stefanhepp/eOrgan/design/parts/Powerswitch Case.FCStd

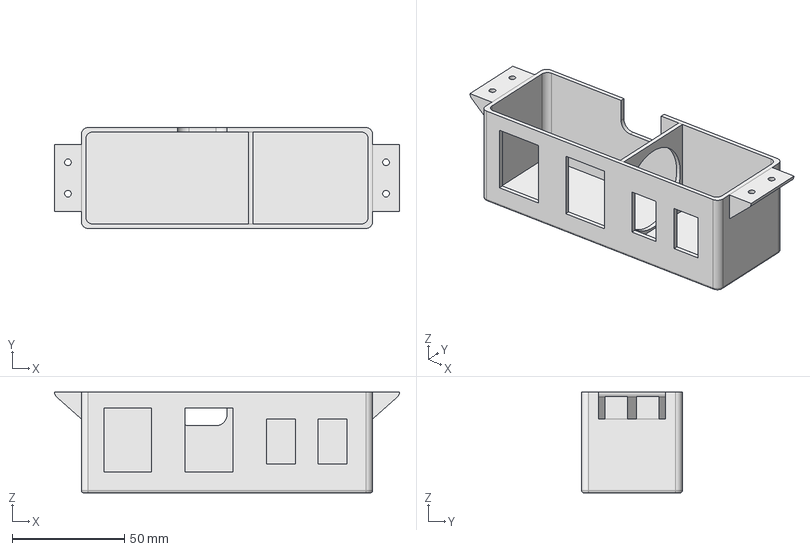
[picture p15: CAD file, 2022-12-17]
design/parts/Powerswitch Case.FCStd
154.0 x 45.0 x 45.0 mm
