stefanhepp/eOrgan/design/parts/Interface Case.FCStd

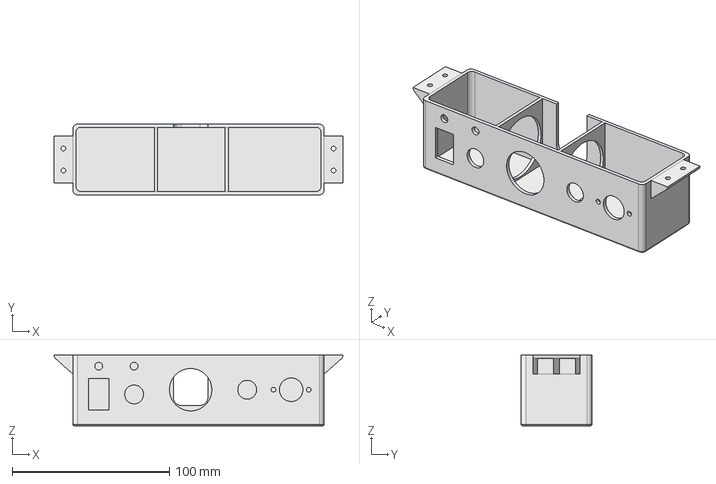
[picture p16: CAD file, 2022-12-17]
design/parts/Interface Case.FCStd
184.0 x 45.0 x 45.0 mm
