stefanhepp/eOrgan/design/parts/Doorknob.FCStd

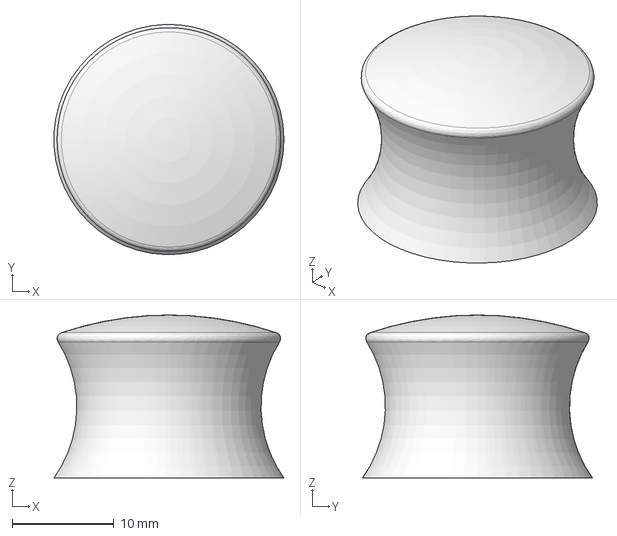
[picture p17: CAD file, 2022-12-17]
design/parts/Doorknob.FCStd
22.6 x 22.6 x 16.0 mm
