stefanhepp/eOrgan/design/parts/Toestop Switch.FCStd

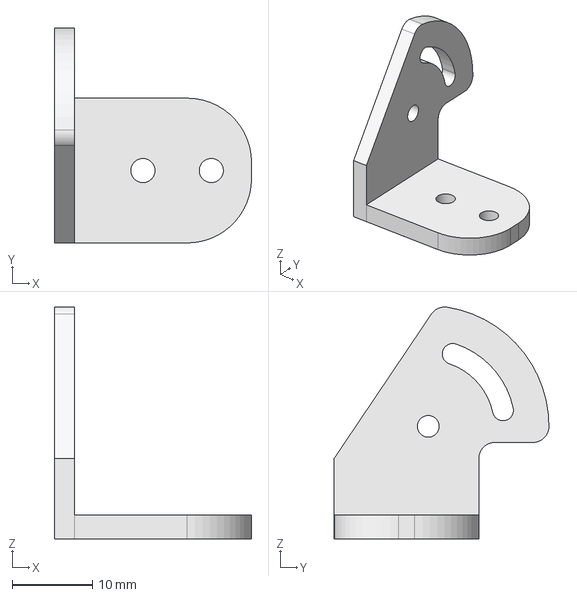
[picture p18: CAD file, 2022-12-17]
design/parts/Toestop Switch.FCStd
24.5 x 26.7 x 28.8 mm
