stefanhepp/eOrgan/design/Panel Inserts.FCStd

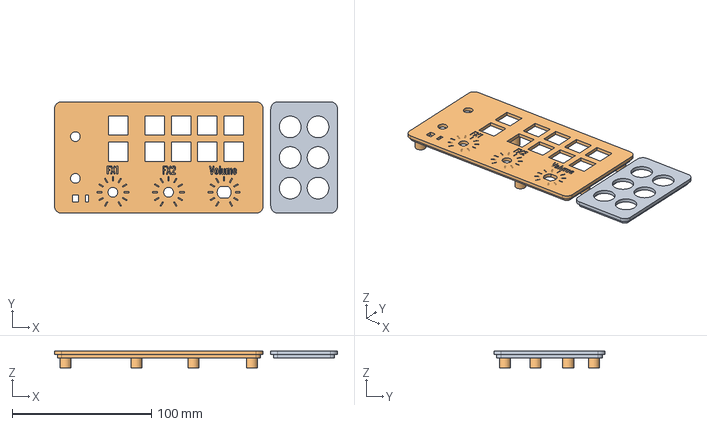
[picture p19: CAD file, 2024-10-20]
design/Panel Inserts.FCStd
203.5 x 80.0 x 12.0 mm
Buttons
MainControl
