stefanhepp/eOrgan/design/Panel Inserts-Buttons.step

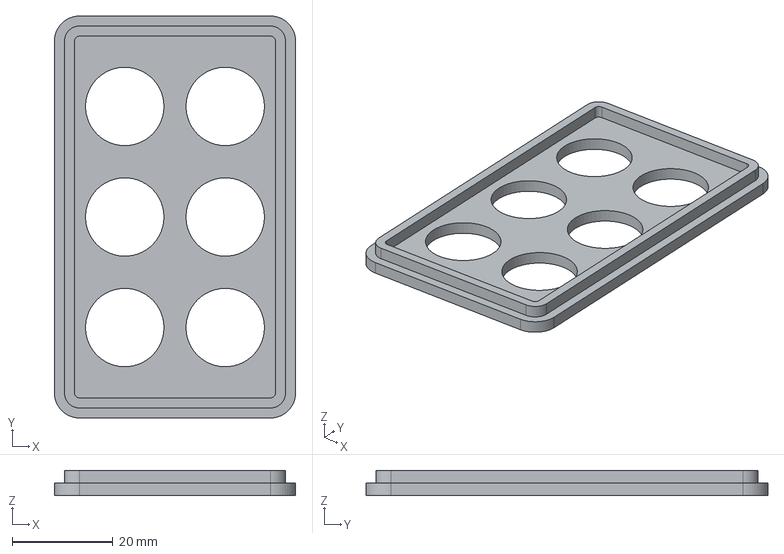
[picture p20: CAD file, 2024-10-18]
design/Panel Inserts-Buttons.step
48.0 x 80.0 x 5.00 mm
