stefanhepp/eOrgan/design/Lock Mount-Body Left.step

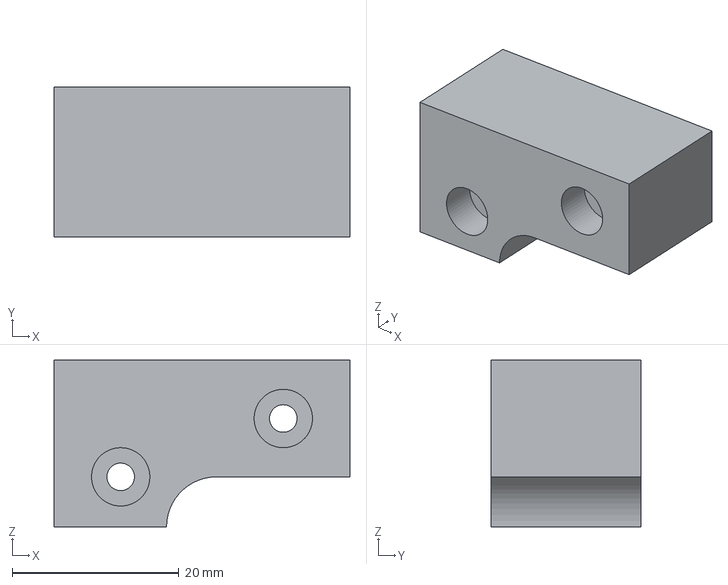
[picture p21: CAD file, 2024-10-08]
design/Lock Mount-Body Left.step
35.5 x 18.0 x 20.0 mm
