stefanhepp/eOrgan/design/Lock Mount-Body Right.step

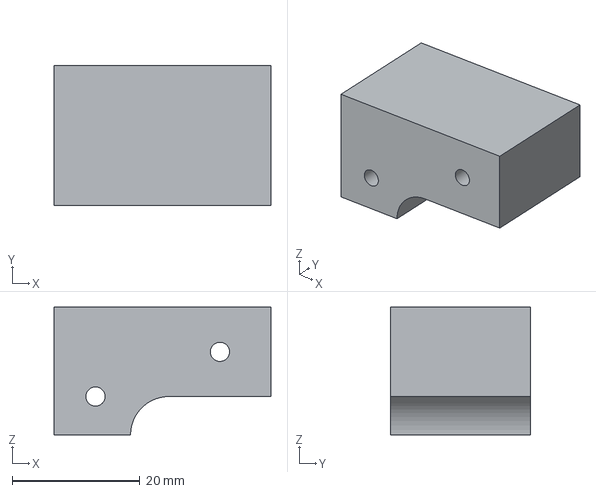
[picture p22: CAD file, 2024-10-08]
design/Lock Mount-Body Right.step
34.0 x 22.0 x 20.0 mm
