stefanhepp/eOrgan/design/PCB Holder.FCStd

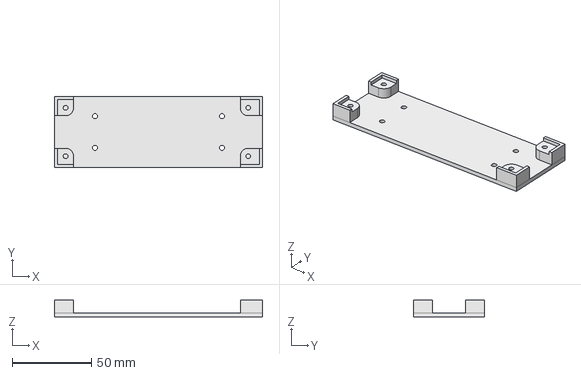
[picture p23: CAD file, 2024-09-07]
design/PCB Holder.FCStd
131.0 x 44.5 x 10.5 mm
