stefanhepp/eOrgan/design/PCB Holder-Technics.step

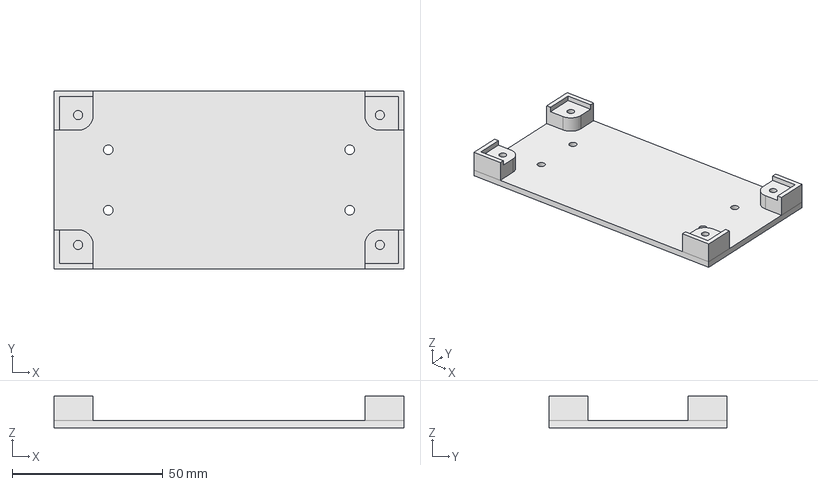
[picture p24: CAD file, 2024-09-07]
design/PCB Holder-Technics.step
116.0 x 59.0 x 10.5 mm
