stefanhepp/eOrgan/design/PCB Holder-LCD.step

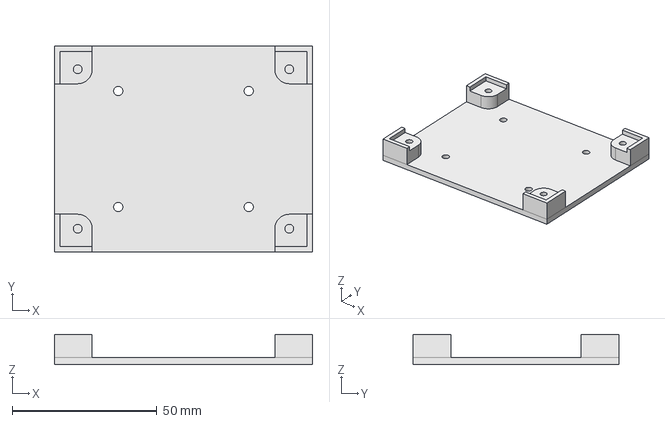
[picture p25: CAD file, 2024-09-07]
design/PCB Holder-LCD.step
89.0 x 71.0 x 10.5 mm
