stefanhepp/eOrgan/design/PCB Holder-150x100.step

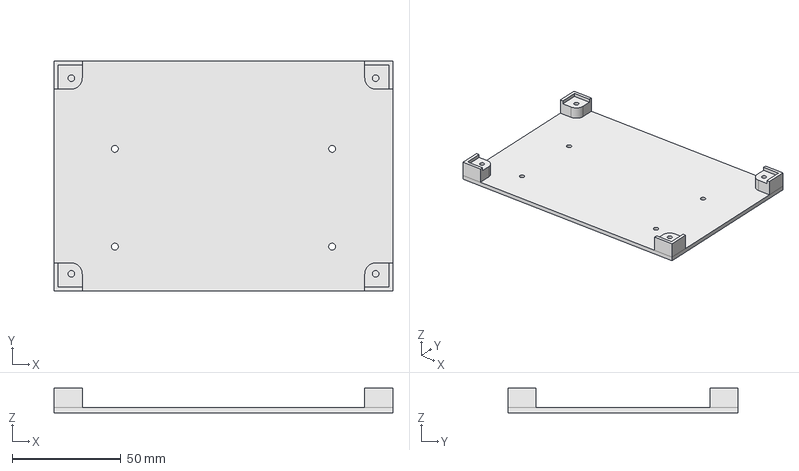
[picture p26: CAD file, 2024-09-07]
design/PCB Holder-150x100.step
156.0 x 106.0 x 11.5 mm
