stefanhepp/eOrgan/design/PCB Holder Technics-Holder 110x53.step

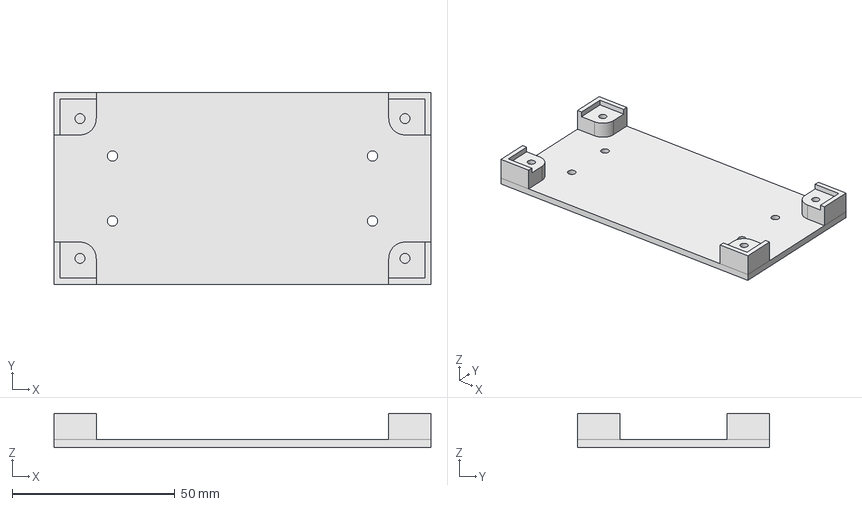
[picture p27: CAD file, 2024-09-02]
design/PCB Holder Technics-Holder 110x53.step
116.0 x 59.0 x 10.5 mm
