stefanhepp/eOrgan/design/ToeStudEncoder Case.FCStd

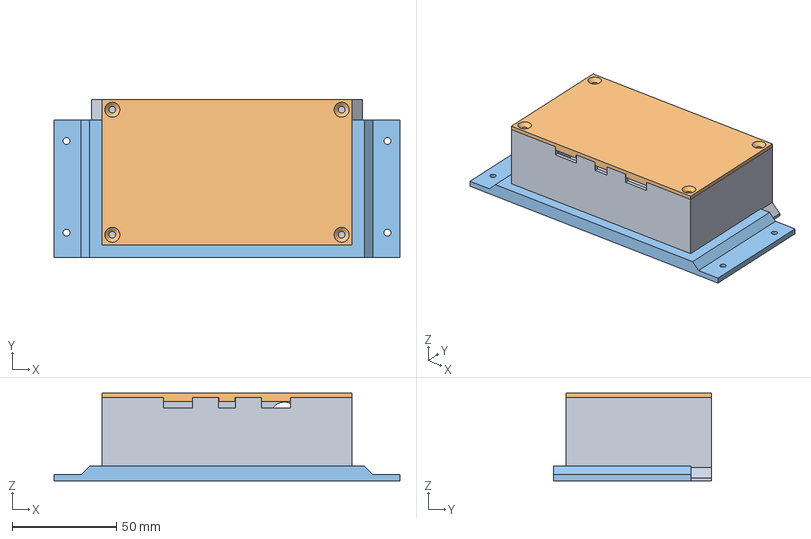
[picture p28: CAD file, 2024-06-30]
design/ToeStudEncoder Case.FCStd
166.0 x 76.0 x 42.0 mm
Case
Lid
Holder
