stefanhepp/eOrgan/design/ToeStudEncoder Case-Lid.step

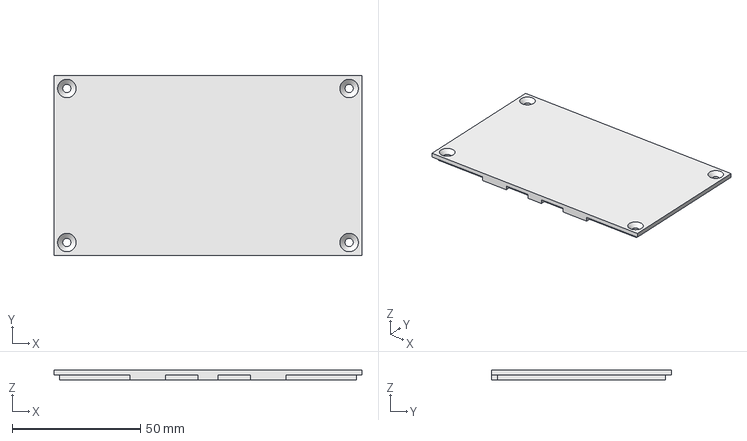
[picture p29: CAD file, 2024-06-30]
design/ToeStudEncoder Case-Lid.step
120.0 x 70.0 x 4.00 mm
