stefanhepp/eOrgan/design/ToeStudEncoder Case-Case.step

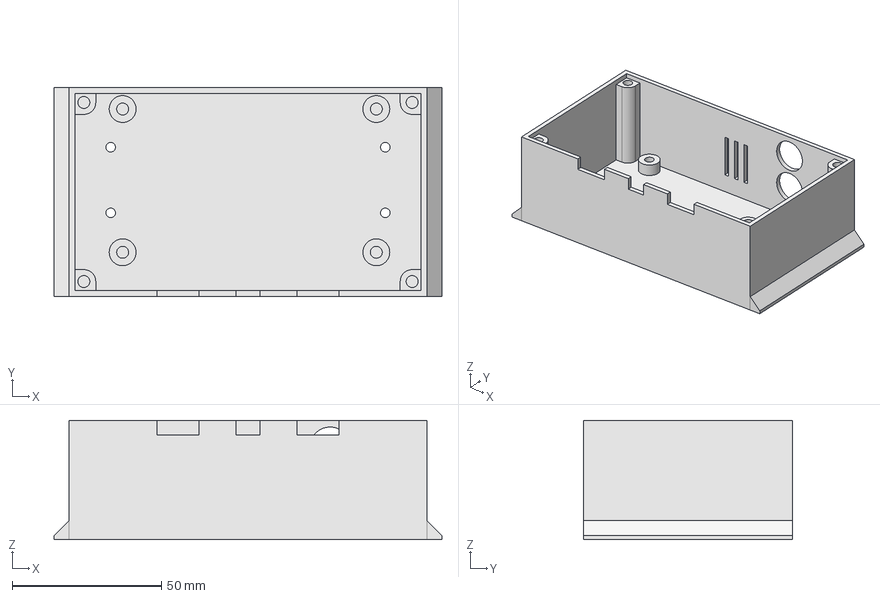
[picture p30: CAD file, 2024-06-30]
design/ToeStudEncoder Case-Case.step
130.0 x 70.0 x 40.0 mm
