stefanhepp/eOrgan/design/ToeStudEncoder Case-Holder.step

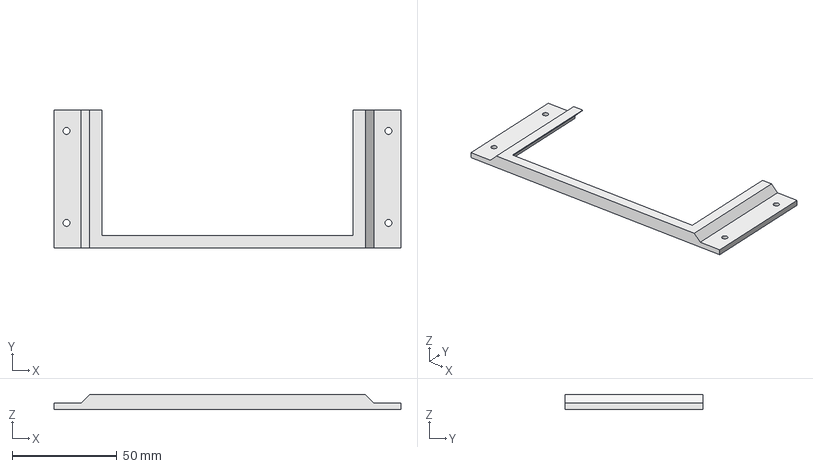
[picture p31: CAD file, 2024-06-30]
design/ToeStudEncoder Case-Holder.step
166.0 x 66.0 x 7.00 mm
