stefanhepp/eOrgan/design/PCB Holder-Base.step

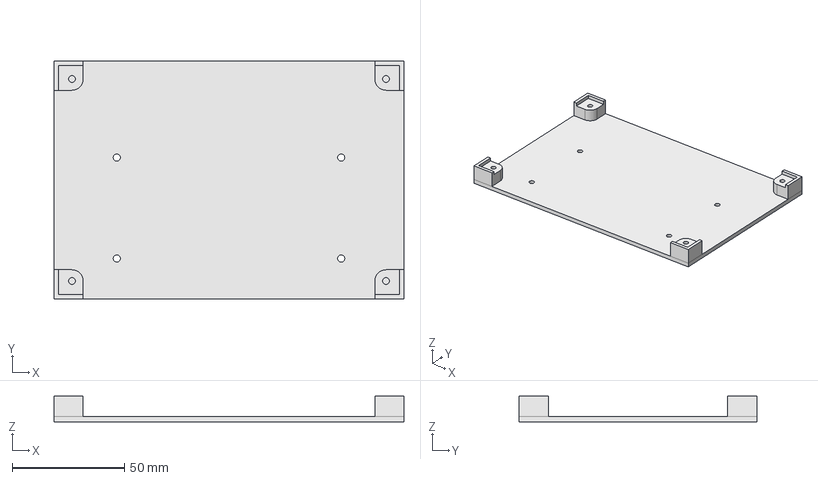
[picture p32: CAD file, 2024-06-30]
design/PCB Holder-Base.step
156.0 x 106.0 x 11.5 mm
