stefanhepp/eOrgan/boards/MIDIController-IO-Boards/MIDIController-IO-Boards.kicad_pcb

## KiCad design boards/MIDIController-IO-Boards/MIDIController-IO-Boards.kicad_pcb (2024-06-30)

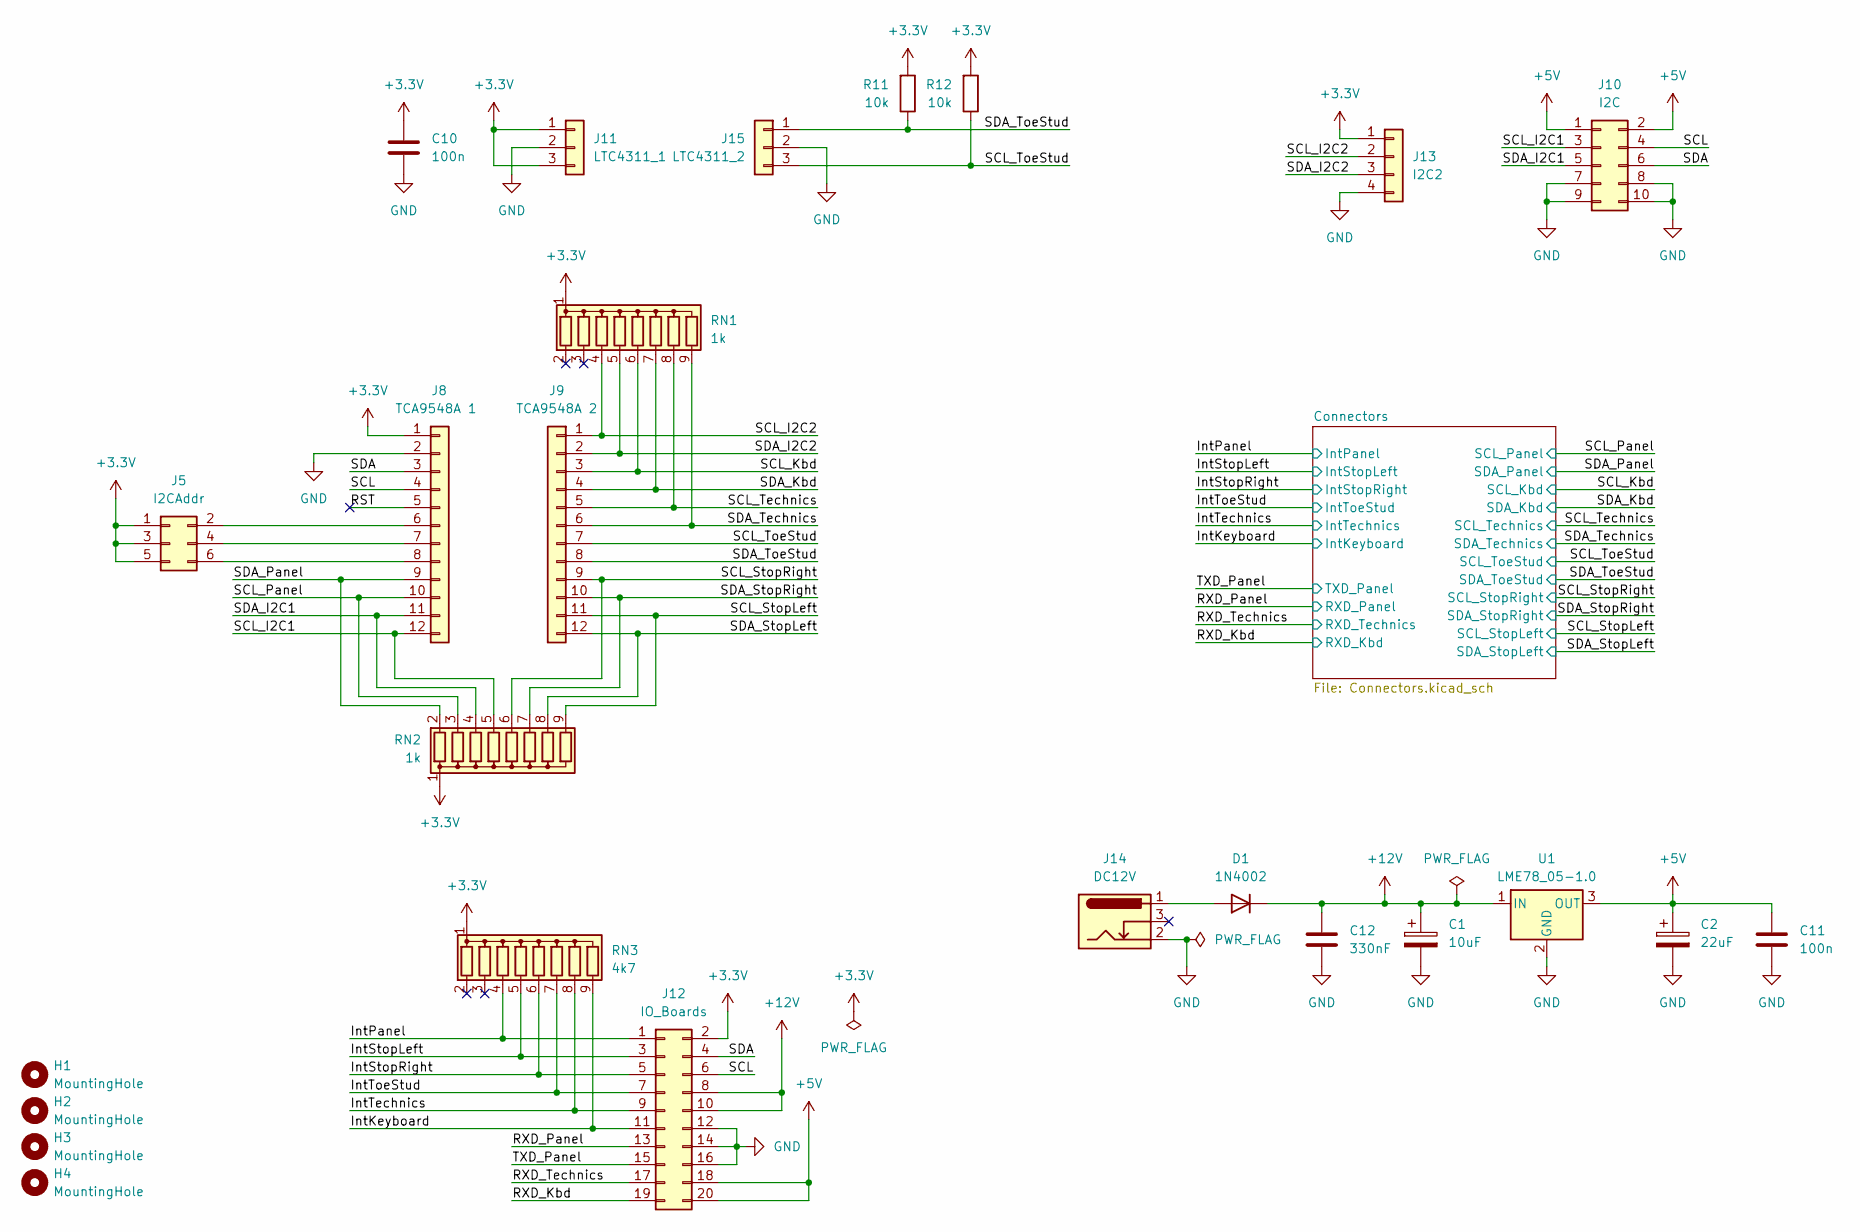
[picture p56: schematic MIDIController-IO-Boards.kicad_sch]

Parts:
C1: 10uF; CP_Radial_D5.0mm_P2.00mm
C2: 22uF; CP_Radial_D8.0mm_P2.50mm
C10, C11: 100n; C_Disc_D5.0mm_W2.5mm_P5.00mm
C12: 330nF; C_Disc_D5.0mm_W2.5mm_P5.00mm
D1: 1N4002; D_DO-41_SOD81_P10.16mm_Horizontal
H1, H2, H3, H4: MountingHole; MountingHole_3.2mm_M3
J5: I2CAddr; PinHeader_2x03_P2.54mm_Vertical
J8: TCA9548A 1; PinSocket_1x12_P2.54mm_Vertical
J9: TCA9548A 2; PinSocket_1x12_P2.54mm_Vertical
J10: I2C; IDC-Header_2x05_P2.54mm_Vertical
J11: LTC4311_1; PinSocket_1x03_P2.54mm_Vertical
J12: IO_Boards; IDC-Header_2x10_P2.54mm_Vertical
J13: I2C2; PinHeader_1x04_P2.54mm_Vertical
J14: DC12V; BarrelJack_Horizontal
J15: LTC4311_2; PinSocket_1x03_P2.54mm_Vertical
R11, R12: 10k; R_Axial_DIN0207_L6.3mm_D2.5mm_P10.16mm_Horizontal
RN1, RN2: 1k; R_Array_SIP9
RN3: 4k7; R_Array_SIP9
U1: LME78_05-1.0; Converter_DCDC_GAPTEC_LME78_05-1.0

Connections:
+3.3V: C10.1, J5.1, J5.3, J5.5, J8.1, J11.1, J11.3, J12.2, J13.1, R11.2, R12.2, RN1.1 (common), RN2.1 (common), RN3.1 (common); also elsewhere on the board
+5V: C2.1, C11.1, J10.1, J10.2, J12.18, J12.20, U1.3 (OUT); also elsewhere on the board
+12V: C1.1, C12.1, D1.1 (K), J12.8, J12.10, U1.1 (IN); also elsewhere on the board
/IntKeyboard: J12.11, RN3.9 (R8); also elsewhere on the board
/IntPanel: J12.1, RN3.4 (R3); also elsewhere on the board
/IntStopLeft: J12.3, RN3.5 (R4); also elsewhere on the board
/IntStopRight: J12.5, RN3.6 (R5); also elsewhere on the board
/IntTechnics: J12.9, RN3.8 (R7); also elsewhere on the board
/IntToeStud: J12.7, RN3.7 (R6); also elsewhere on the board
/RST: J8.5
/RXD_Kbd: J12.19; also elsewhere on the board
/RXD_Panel: J12.13; also elsewhere on the board
/RXD_Technics: J12.17; also elsewhere on the board
/SCL: J8.4, J10.4, J12.6
/SCL_I2C1: J8.12, J10.3, RN2.5 (R4)
/SCL_I2C2: J9.1, J13.2, RN1.4 (R3)
/SCL_Kbd: J9.3, RN1.6 (R5); also elsewhere on the board
/SCL_Panel: J8.10, RN2.3 (R2); also elsewhere on the board
/SCL_StopLeft: J9.11, RN2.9 (R8); also elsewhere on the board
/SCL_StopRight: J9.9, RN2.6 (R5); also elsewhere on the board
/SCL_Technics: J9.5, RN1.8 (R7); also elsewhere on the board
/SCL_ToeStud: J9.7, J15.3, R12.1; also elsewhere on the board
/SDA: J8.3, J10.6, J12.4
/SDA_I2C1: J8.11, J10.5, RN2.4 (R3)
/SDA_I2C2: J9.2, J13.3, RN1.5 (R4)
/SDA_Kbd: J9.4, RN1.7 (R6); also elsewhere on the board
/SDA_Panel: J8.9, RN2.2 (R1); also elsewhere on the board
/SDA_StopLeft: J9.12, RN2.8 (R7); also elsewhere on the board
/SDA_StopRight: J9.10, RN2.7 (R6); also elsewhere on the board
/SDA_Technics: J9.6, RN1.9 (R8); also elsewhere on the board
/SDA_ToeStud: J9.8, J15.1, R11.1; also elsewhere on the board
/TXD_Panel: J12.15; also elsewhere on the board
GND: C1.2, C2.2, C10.2, C11.2, C12.2, J8.2, J10.7, J10.8, J10.9, J10.10, J11.2, J12.12, J12.14, J12.16, J13.4, J14.2, J15.2, U1.2 (GND); also elsewhere on the board
unnamed: D1.2 (A), J14.1
unnamed: J5.2, J8.6
unnamed: J5.4, J8.7
unnamed: J5.6, J8.8

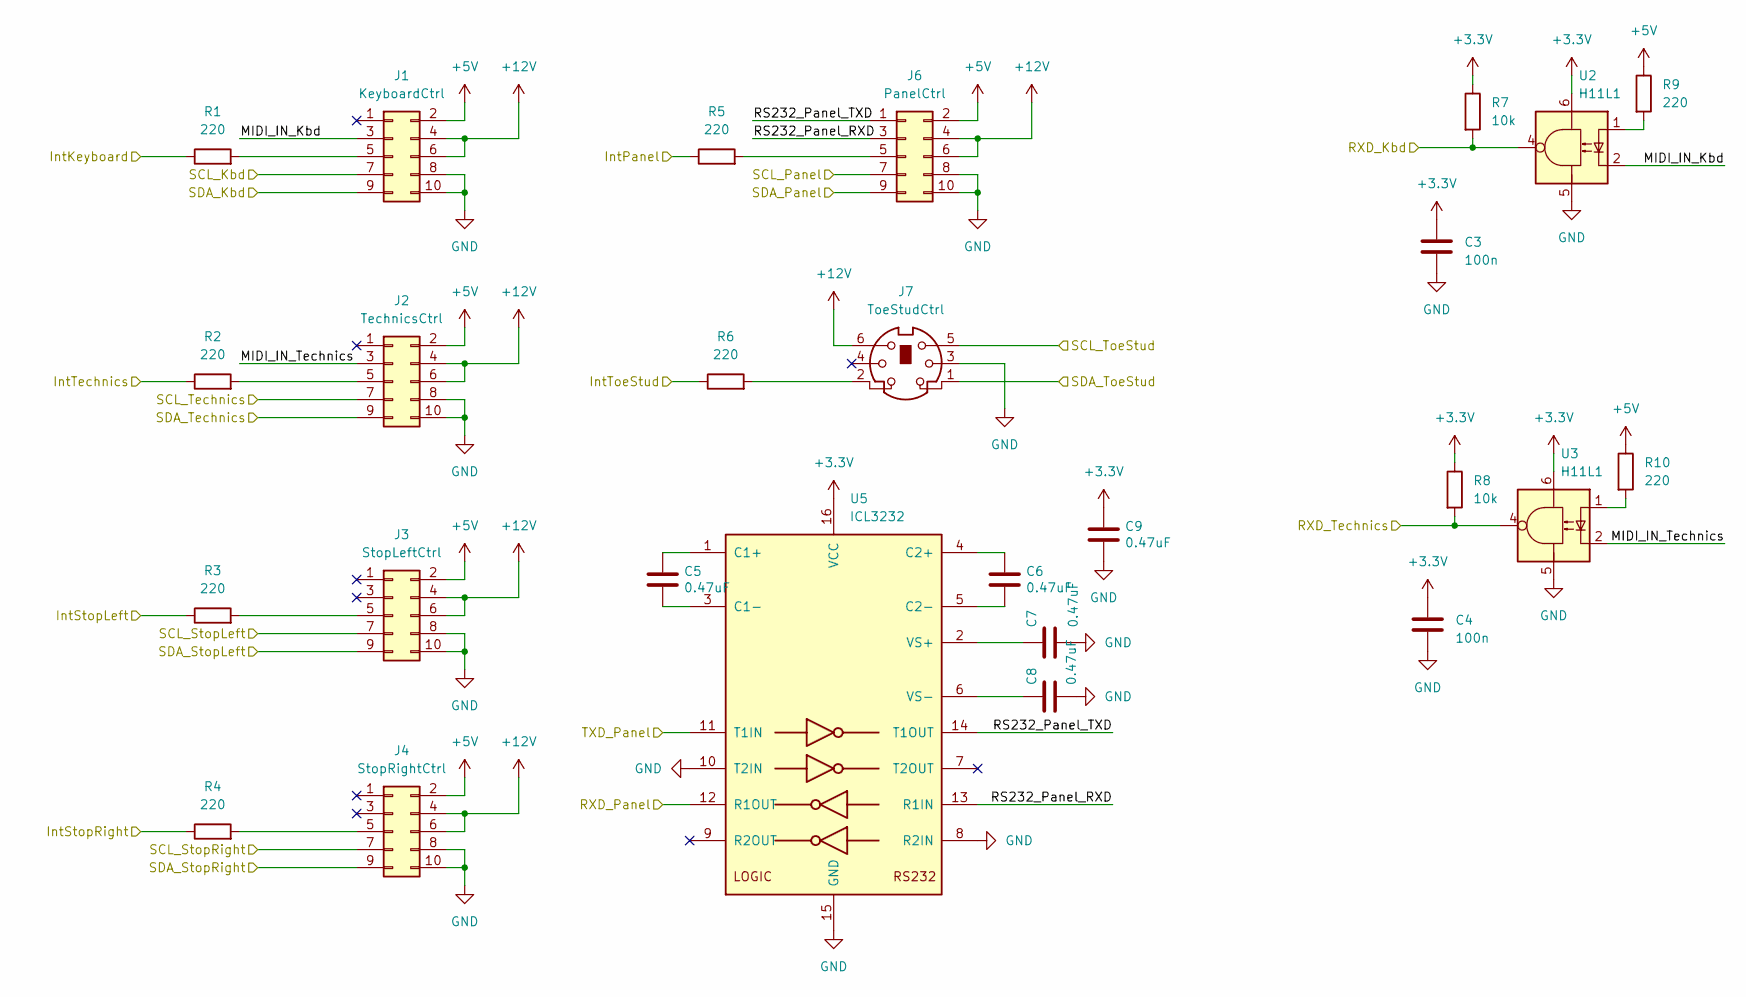
[picture p57: schematic Connectors.kicad_sch]

Parts:
C3, C4: 100n; C_Disc_D5.0mm_W2.5mm_P5.00mm
C5, C6, C7, C8, C9: 0.47uF; C_Rect_L7.0mm_W3.5mm_P5.00mm; Voltage 50V
J1: KeyboardCtrl; IDC-Header_2x05_P2.54mm_Horizontal
J2: TechnicsCtrl; IDC-Header_2x05_P2.54mm_Horizontal
J3: StopLeftCtrl; IDC-Header_2x05_P2.54mm_Horizontal
J4: StopRightCtrl; IDC-Header_2x05_P2.54mm_Horizontal
J6: PanelCtrl; IDC-Header_2x05_P2.54mm_Horizontal
J7: ToeStudCtrl; MiniDIN TE_5749180-1
R1, R2, R3, R4, R5, R6, R9, R10: 220; R_Axial_DIN0207_L6.3mm_D2.5mm_P10.16mm_Horizontal
R7, R8: 10k; R_Axial_DIN0207_L6.3mm_D2.5mm_P10.16mm_Horizontal
U2, U3: H11L1; DIP-6_W7.62mm
U5: ICL3232; DIP-16_W7.62mm

Connections:
+3.3V: C3.1, C4.1, C9.1, R7.1, R8.1, U2.6, U3.6, U5.16 (VCC); also elsewhere on the board
+5V: J1.2, J2.2, J3.2, J4.2, J6.2, R9.1, R10.1; also elsewhere on the board
+12V: J1.4, J1.6, J2.4, J2.6, J3.4, J3.6, J4.4, J4.6, J6.4, J6.6, J7.6; also elsewhere on the board
/Connectors/MIDI_IN_Kbd: J1.3, U2.2
/Connectors/MIDI_IN_Technics: J2.3, U3.2
/Connectors/RS232_Panel_RXD: J6.3, U5.13 (R1IN)
/Connectors/RS232_Panel_TXD: J6.1, U5.14 (T1OUT)
/IntKeyboard: R1.1; also elsewhere on the board
/IntPanel: R5.1; also elsewhere on the board
/IntStopLeft: R3.1; also elsewhere on the board
/IntStopRight: R4.1; also elsewhere on the board
/IntTechnics: R2.1; also elsewhere on the board
/IntToeStud: R6.1; also elsewhere on the board
/RXD_Kbd: R7.2, U2.4; also elsewhere on the board
/RXD_Panel: U5.12 (R1OUT); also elsewhere on the board
/RXD_Technics: R8.2, U3.4; also elsewhere on the board
/SCL_Kbd: J1.7; also elsewhere on the board
/SCL_Panel: J6.7; also elsewhere on the board
/SCL_StopLeft: J3.7; also elsewhere on the board
/SCL_StopRight: J4.7; also elsewhere on the board
/SCL_Technics: J2.7; also elsewhere on the board
/SCL_ToeStud: J7.5; also elsewhere on the board
/SDA_Kbd: J1.9; also elsewhere on the board
/SDA_Panel: J6.9; also elsewhere on the board
/SDA_StopLeft: J3.9; also elsewhere on the board
/SDA_StopRight: J4.9; also elsewhere on the board
/SDA_Technics: J2.9; also elsewhere on the board
/SDA_ToeStud: J7.1; also elsewhere on the board
/TXD_Panel: U5.11 (T1IN); also elsewhere on the board
GND: C3.2, C4.2, C7.2, C8.2, C9.2, J1.8, J1.10, J2.8, J2.10, J3.8, J3.10, J4.8, J4.10, J6.8, J6.10, J7.3, U2.5, U3.5, U5.8 (R2IN), U5.10 (T2IN), U5.15 (GND); also elsewhere on the board
unnamed: J1.5, R1.2
unnamed: J2.5, R2.2
unnamed: J3.5, R3.2
unnamed: J4.5, R4.2
unnamed: J6.5, R5.2
unnamed: J7.2, R6.2
unnamed: R9.2, U2.1
unnamed: R10.2, U3.1
unnamed: C5.1, U5.1 (C1+)
unnamed: C5.2, U5.3 (C1-)
unnamed: C6.1, U5.4 (C2+)
unnamed: C6.2, U5.5 (C2-)
unnamed: C7.1, U5.2 (VS+)
unnamed: C8.1, U5.6 (VS-)

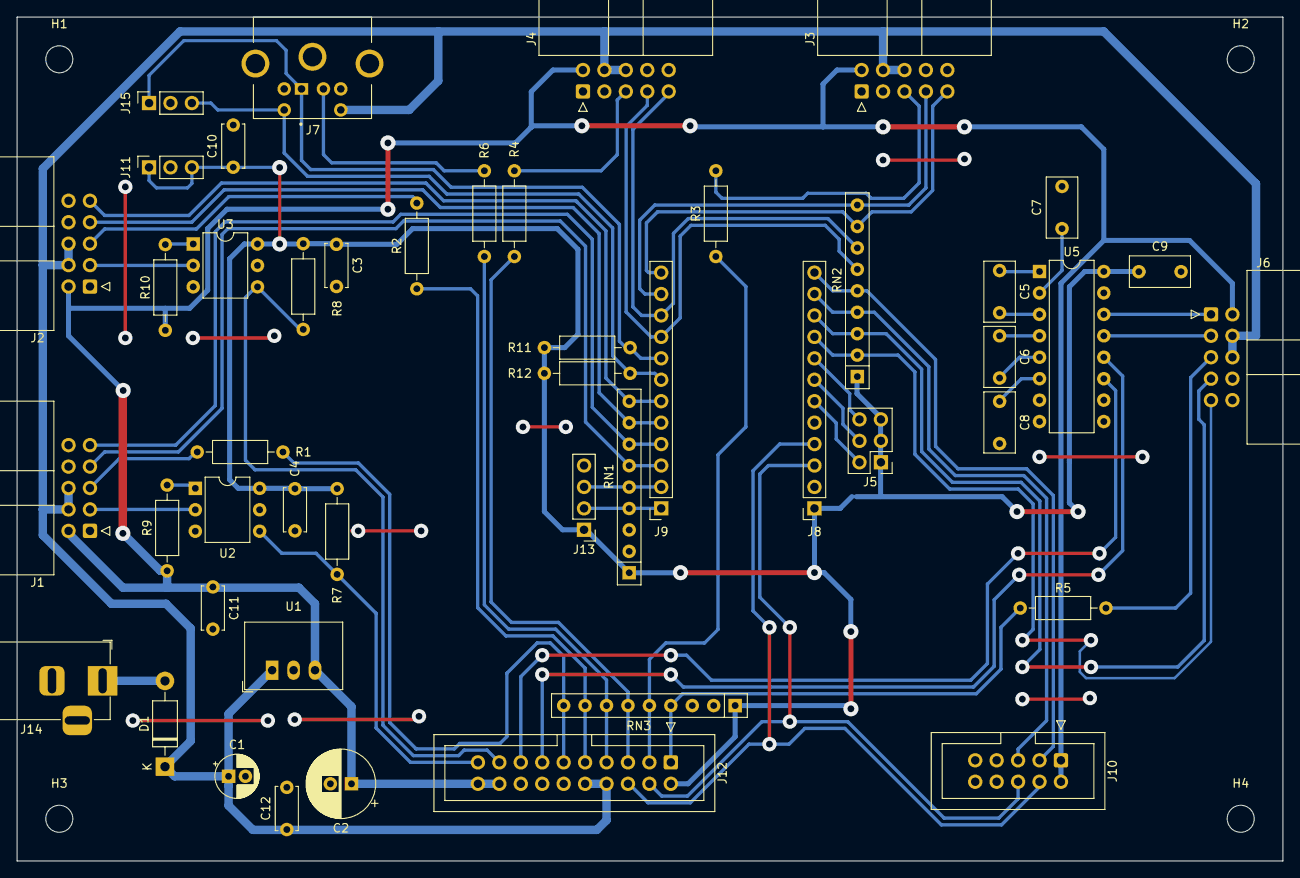
[picture p58: board MIDIController-IO-Boards.kicad_pcb from above]

Board: 2 copper layers, 150.0 x 100.0 mm, 51 parts (0 on the bottom side), 54 nets.
