stefanhepp/eOrgan/boards/KeyboardEncoder/KeyboardEncoder.kicad_pcb

## KiCad design boards/KeyboardEncoder/KeyboardEncoder.kicad_pcb (2024-05-18)

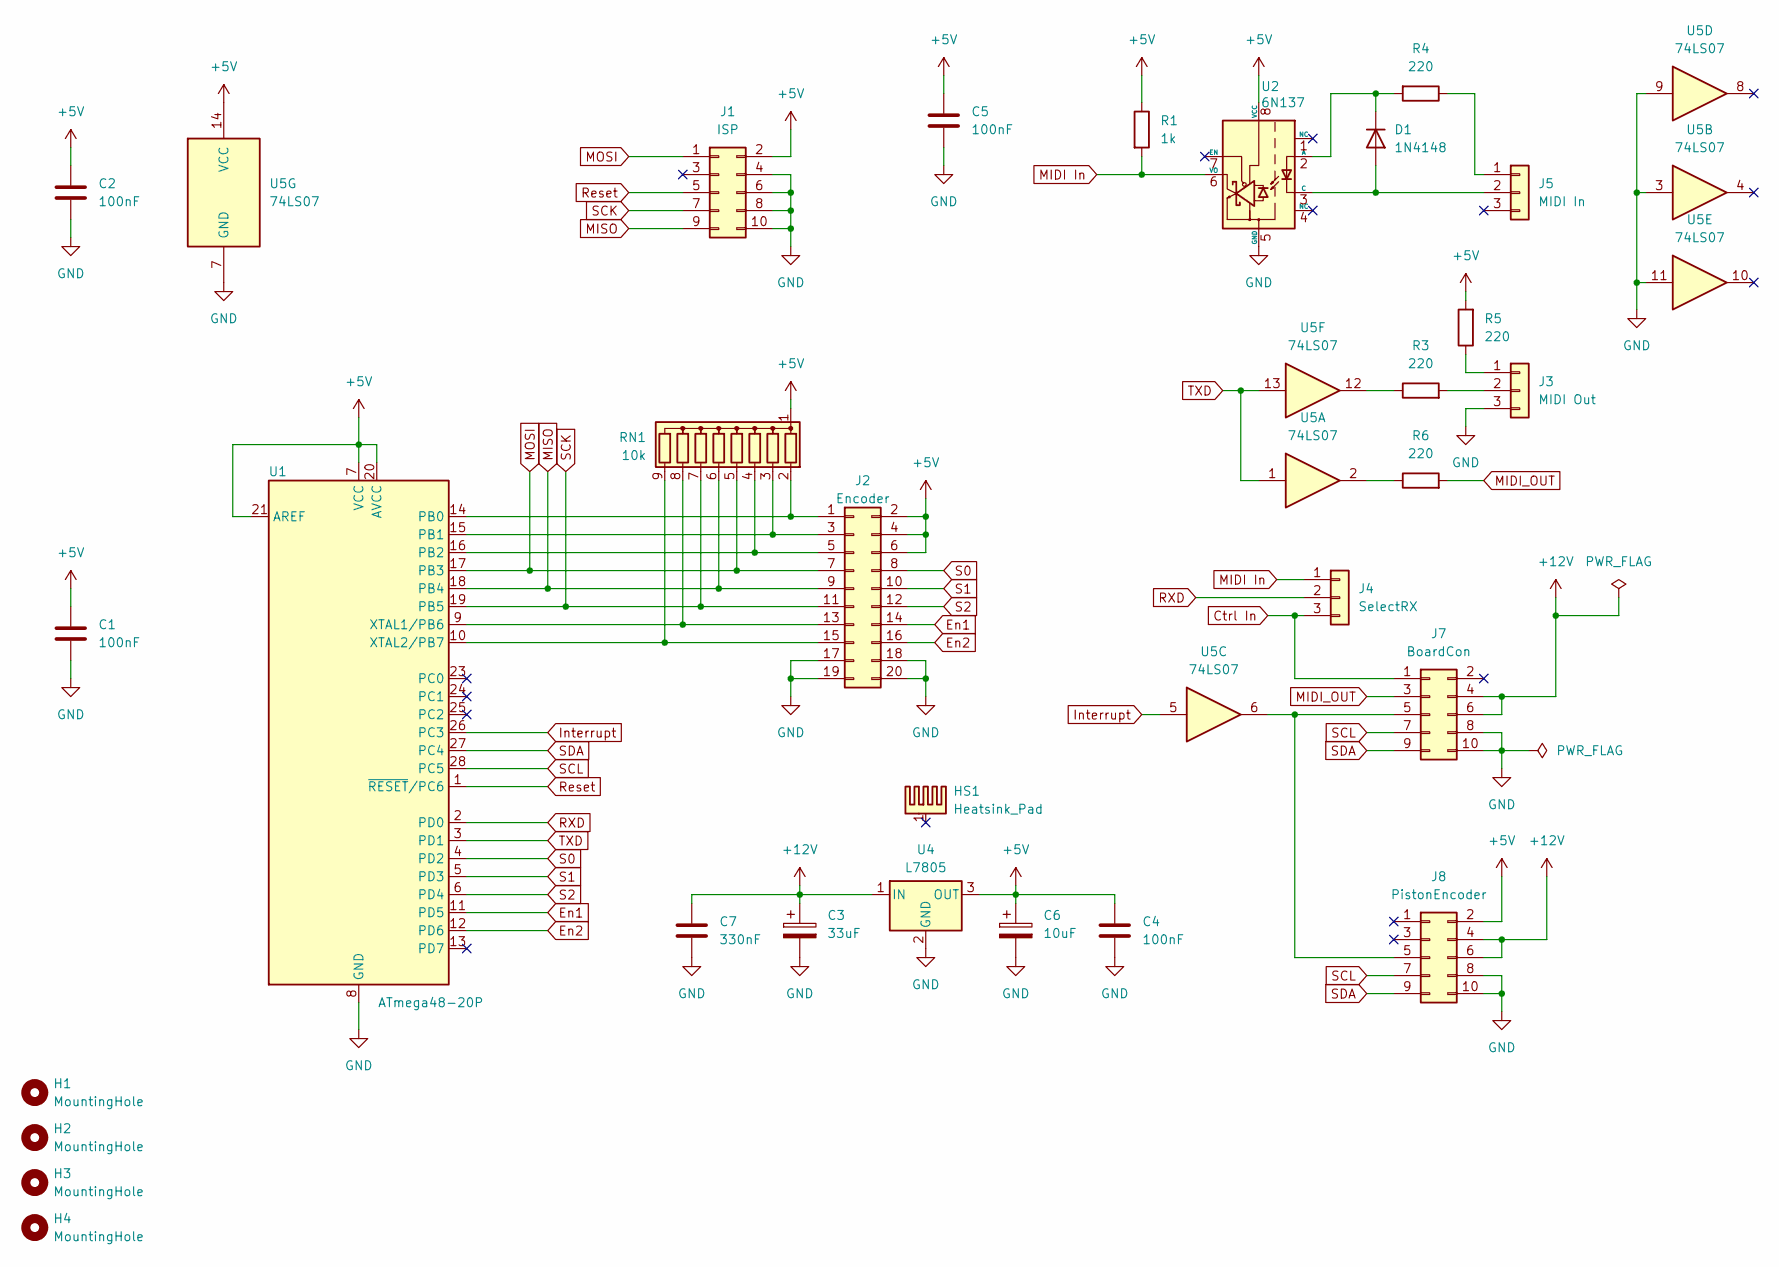
[picture p59: schematic KeyboardEncoder.kicad_sch]

Parts:
C1, C2, C4, C5: 100nF; C_Disc_D4.3mm_W1.9mm_P5.00mm
C3: 33uF; CP_Radial_D7.5mm_P2.50mm
C6: 10uF; CP_Radial_D5.0mm_P2.00mm
C7: 330nF; C_Disc_D4.3mm_W1.9mm_P5.00mm
D1: 1N4148; D_DO-35_SOD27_P7.62mm_Horizontal
H1, H2, H3, H4: MountingHole; MountingHole_3.2mm_M3
HS1: Heatsink_Pad; Heatsink_Aavid_TO-220_H12.7mm
J1: ISP; IDC-Header_2x05_P2.54mm_Horizontal
J2: Encoder; IDC-Header_2x10_P2.54mm_Horizontal
J3: MIDI Out; PinHeader_1x03_P2.54mm_Vertical
J4: SelectRX; PinHeader_1x03_P2.54mm_Vertical
J5: MIDI In; PinHeader_1x03_P2.54mm_Vertical
J7: BoardCon; IDC-Header_2x05_P2.54mm_Horizontal
J8: PistonEncoder; IDC-Header_2x05_P2.54mm_Vertical
R1: 1k; R_Axial_DIN0207_L6.3mm_D2.5mm_P2.54mm_Vertical
R3, R4, R5, R6: 220; R_Axial_DIN0207_L6.3mm_D2.5mm_P10.16mm_Horizontal
RN1: 10k; R_Array_SIP9
U1: ATmega48-20P; DIP-28_W7.62mm
U2: 6N137; DIP-8_W7.62mm
U4: L7805; TO-220-3_Vertical
U5: 74LS07; DIP-14_W7.62mm

Connections:
+5V: C1.1, C2.1, C4.1, C5.1, C6.1, J1.2, J2.2, J2.4, J2.6, J8.2, R1.1, R5.2, RN1.1 (common), U1.7 (VCC), U1.20 (AVCC), U1.21 (AREF), U2.8 (VCC), U4.3 (OUT), U5.14 (VCC)
+12V: C3.1, C7.1, J7.4, J7.6, J8.4, J8.6, U4.1 (IN)
Ctrl In: J4.3, J7.1
En1: J2.14, U1.11 (PD5)
En2: J2.16, U1.12 (PD6)
GND: C1.2, C2.2, C3.2, C4.2, C5.2, C6.2, C7.2, J1.4, J1.6, J1.8, J1.10, J2.17, J2.18, J2.19, J2.20, J3.3, J7.8, J7.10, J8.8, J8.10, U1.8 (GND), U1.22 (GND), U2.5 (GND), U4.2 (GND), U5.3, U5.7 (GND), U5.9, U5.11
Interrupt: U1.26 (PC3), U5.5
MIDI In: J4.1, R1.2, U2.6 (VO)
MIDI_OUT: J7.3, R6.2
MISO: J1.9, J2.9, RN1.6 (R5), U1.18 (PB4)
MOSI: J1.1, J2.7, RN1.5 (R4), U1.17 (PB3)
unnamed: D1.2 (A), J5.2, U2.3 (C)
unnamed: D1.1 (K), R4.2, U2.2 (A)
unnamed: J2.1, RN1.2 (R1), U1.14 (PB0)
unnamed: J2.3, RN1.3 (R2), U1.15 (PB1)
unnamed: J2.5, RN1.4 (R3), U1.16 (PB2)
unnamed: J2.13, RN1.8 (R7), U1.9 (XTAL1/PB6)
unnamed: J2.15, RN1.9 (R8), U1.10 (XTAL2/PB7)
unnamed: J3.1, R5.1
unnamed: J3.2, R3.2
unnamed: J5.1, R4.1
unnamed: J7.5, J8.5, U5.6
unnamed: R3.1, U5.12
unnamed: R6.1, U5.2
RXD: J4.2, U1.2 (PD0)
Reset: J1.5, U1.1 (~RESET/PC6)
S0: J2.8, U1.4 (PD2)
S1: J2.10, U1.5 (PD3)
S2: J2.12, U1.6 (PD4)
SCK: J1.7, J2.11, RN1.7 (R6), U1.19 (PB5)
SCL: J7.7, J8.7, U1.28 (PC5)
SDA: J7.9, J8.9, U1.27 (PC4)
TXD: U1.3 (PD1), U5.1, U5.13

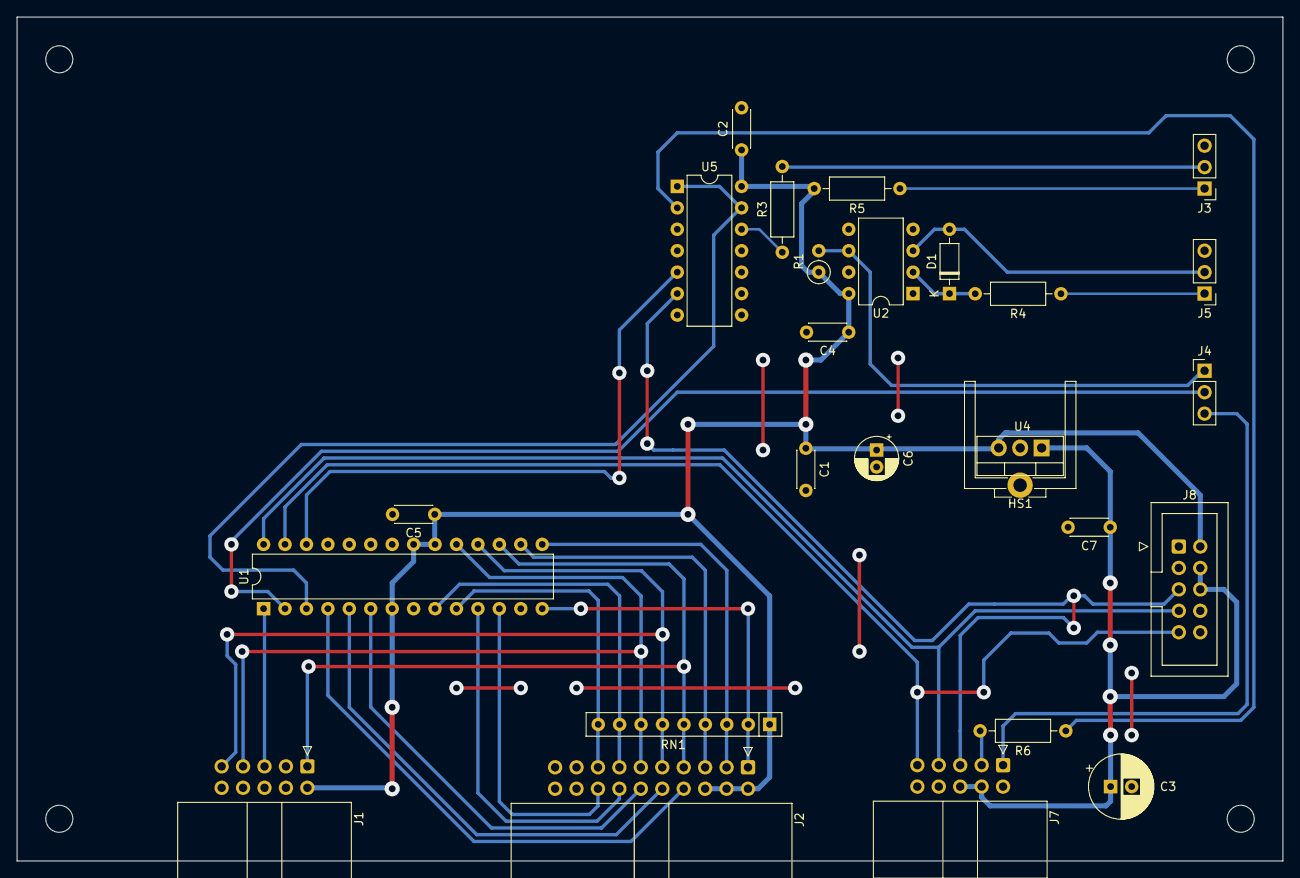
[picture p60: board KeyboardEncoder.kicad_pcb from above]

Board: 2 copper layers, 150.0 x 100.0 mm, 30 parts (0 on the bottom side), 33 nets.
