stefanhepp/eOrgan/boards/PistonEncoder/PistonEncoder.kicad_pcb

## KiCad design boards/PistonEncoder/PistonEncoder.kicad_pcb (2024-05-18)

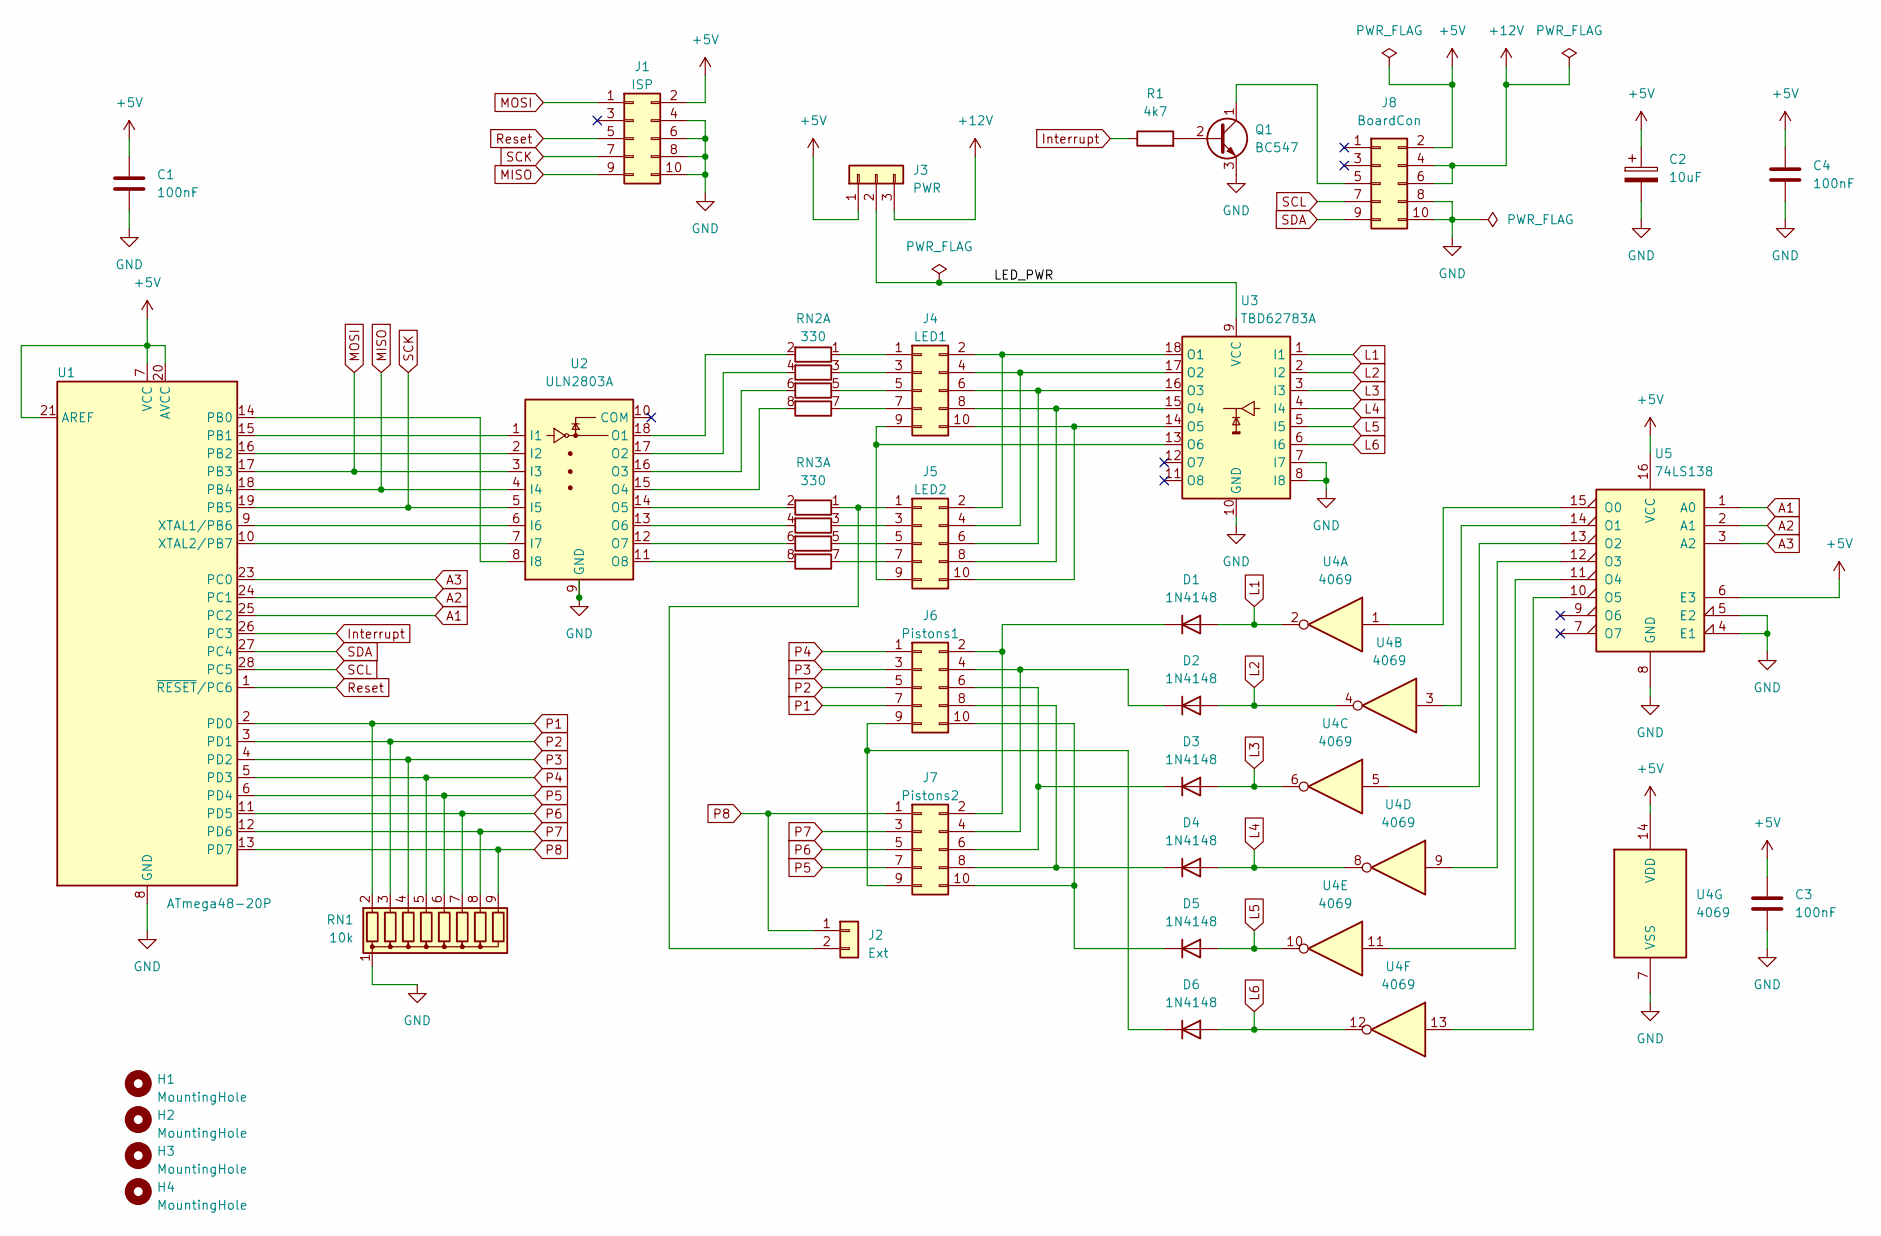
[picture p61: schematic PistonEncoder.kicad_sch]

Parts:
C1, C3, C4: 100nF; C_Disc_D4.3mm_W1.9mm_P5.00mm
C2: 10uF; C_Radial_D5.0mm_H11.0mm_P2.00mm
D1, D2, D3, D4, D5, D6: 1N4148; D_DO-35_SOD27_P7.62mm_Horizontal
H1, H2, H3, H4: MountingHole; MountingHole_3.2mm_M3
J1: ISP; IDC-Header_2x05_P2.54mm_Vertical
J2: Ext; PinHeader_1x02_P2.54mm_Vertical
J3: PWR; PinHeader_1x03_P2.54mm_Vertical
J4: LED1; IDC-Header_2x05_P2.54mm_Vertical
J5: LED2; IDC-Header_2x05_P2.54mm_Vertical
J6: Pistons1; IDC-Header_2x05_P2.54mm_Vertical
J7: Pistons2; IDC-Header_2x05_P2.54mm_Vertical
J8: BoardCon; IDC-Header_2x05_P2.54mm_Vertical
Q1: BC547; TO-92L_Inline_Wide
R1: 4k7; R_Axial_DIN0207_L6.3mm_D2.5mm_P10.16mm_Horizontal
RN1: 10k; R_Array_SIP9
RN2, RN3: 330; R_Array_SIP8
U1: ATmega48-20P; DIP-28_W7.62mm
U2: ULN2803A; DIP-18_W7.62mm
U3: TBD62783A; DIP-18_W7.62mm
U4: 4069; DIP-14_W7.62mm
U5: 74LS138; DIP-16_W7.62mm

Connections:
+5V: C1.1, C2.1, C3.1, C4.1, J1.2, J3.1, J8.2, U1.7 (VCC), U1.20 (AVCC), U1.21 (AREF), U4.14 (VDD), U5.6 (E3), U5.16 (VCC)
+12V: J3.3, J8.4, J8.6
/LED_PWR: J3.2, U3.9 (VCC)
A1: U1.25 (PC2), U5.1 (A0)
A2: U1.24 (PC1), U5.2 (A1)
A3: U1.23 (PC0), U5.3 (A2)
GND: C1.2, C2.2, C3.2, C4.2, J1.4, J1.6, J1.8, J1.10, J8.8, J8.10, Q1.3 (E), RN1.1 (common), U1.8 (GND), U1.22 (GND), U2.9 (GND), U3.7 (I7), U3.8 (I8), U3.10 (GND), U4.7 (VSS), U5.4 (E1), U5.5 (E2), U5.8 (GND)
Interrupt: R1.1, U1.26 (PC3)
L1: D1.2 (A), U3.1 (I1), U4.2
L2: D2.2 (A), U3.2 (I2), U4.4
L3: D3.2 (A), U3.3 (I3), U4.6
L4: D4.2 (A), U3.4 (I4), U4.8
L5: D5.2 (A), U3.5 (I5), U4.10
L6: D6.2 (A), U3.6 (I6), U4.12
MISO: J1.9, U1.18 (PB4), U2.4 (I4)
MOSI: J1.1, U1.17 (PB3), U2.3 (I3)
unnamed: D1.1 (K), J6.2, J7.2
unnamed: D2.1 (K), J6.4, J7.4
unnamed: D3.1 (K), J6.6, J7.6
unnamed: D4.1 (K), J6.8, J7.8
unnamed: D5.1 (K), J6.10, J7.10
unnamed: D6.1 (K), J6.9, J7.9
unnamed: J2.2, J5.1, RN3.1 (R1.1)
unnamed: J4.1, RN2.1 (R1.1)
unnamed: J4.2, J5.2, U3.18 (O1)
unnamed: J4.3, RN2.3 (R2.1)
unnamed: J4.4, J5.4, U3.17 (O2)
unnamed: J4.5, RN2.5 (R3.1)
unnamed: J4.6, J5.6, U3.16 (O3)
unnamed: J4.7, RN2.7 (R4.1)
unnamed: J4.8, J5.8, U3.15 (O4)
unnamed: J4.9, J5.9, U3.13 (O6)
unnamed: J4.10, J5.10, U3.14 (O5)
unnamed: J5.3, RN3.3 (R2.1)
unnamed: J5.5, RN3.5 (R3.1)
unnamed: J5.7, RN3.7 (R4.1)
unnamed: J8.5, Q1.1 (C)
unnamed: Q1.2 (B), R1.2
unnamed: RN2.2 (R1.2), U2.18 (O1)
unnamed: RN2.4 (R2.2), U2.17 (O2)
unnamed: RN2.6 (R3.2), U2.16 (O3)
unnamed: RN2.8 (R4.2), U2.15 (O4)
unnamed: RN3.2 (R1.2), U2.14 (O5)
unnamed: RN3.4 (R2.2), U2.13 (O6)
unnamed: RN3.6 (R3.2), U2.12 (O7)
unnamed: RN3.8 (R4.2), U2.11 (O8)
unnamed: U1.14 (PB0), U2.8 (I8)
unnamed: U1.15 (PB1), U2.1 (I1)
unnamed: U1.16 (PB2), U2.2 (I2)
unnamed: U1.9 (XTAL1/PB6), U2.6 (I6)
unnamed: U1.10 (XTAL2/PB7), U2.7 (I7)
unnamed: U4.1, U5.15 (O0)
unnamed: U4.3, U5.14 (O1)
unnamed: U4.5, U5.13 (O2)
unnamed: U4.9, U5.12 (O3)
unnamed: U4.11, U5.11 (O4)
unnamed: U4.13, U5.10 (O5)
P1: J6.7, RN1.2 (R1), U1.2 (PD0)
P2: J6.5, RN1.3 (R2), U1.3 (PD1)
P3: J6.3, RN1.4 (R3), U1.4 (PD2)
P4: J6.1, RN1.5 (R4), U1.5 (PD3)
P5: J7.7, RN1.6 (R5), U1.6 (PD4)
P6: J7.5, RN1.7 (R6), U1.11 (PD5)
P7: J7.3, RN1.8 (R7), U1.12 (PD6)
P8: J2.1, J7.1, RN1.9 (R8), U1.13 (PD7)
Reset: J1.5, U1.1 (~RESET/PC6)
SCK: J1.7, U1.19 (PB5), U2.5 (I5)
SCL: J8.7, U1.28 (PC5)
SDA: J8.9, U1.27 (PC4)
