stefanhepp/eOrgan/boards/PistonEncoder/PistonEncoder.kicad_pcb

## KiCad design boards/PistonEncoder/PistonEncoder.kicad_pcb (continued)

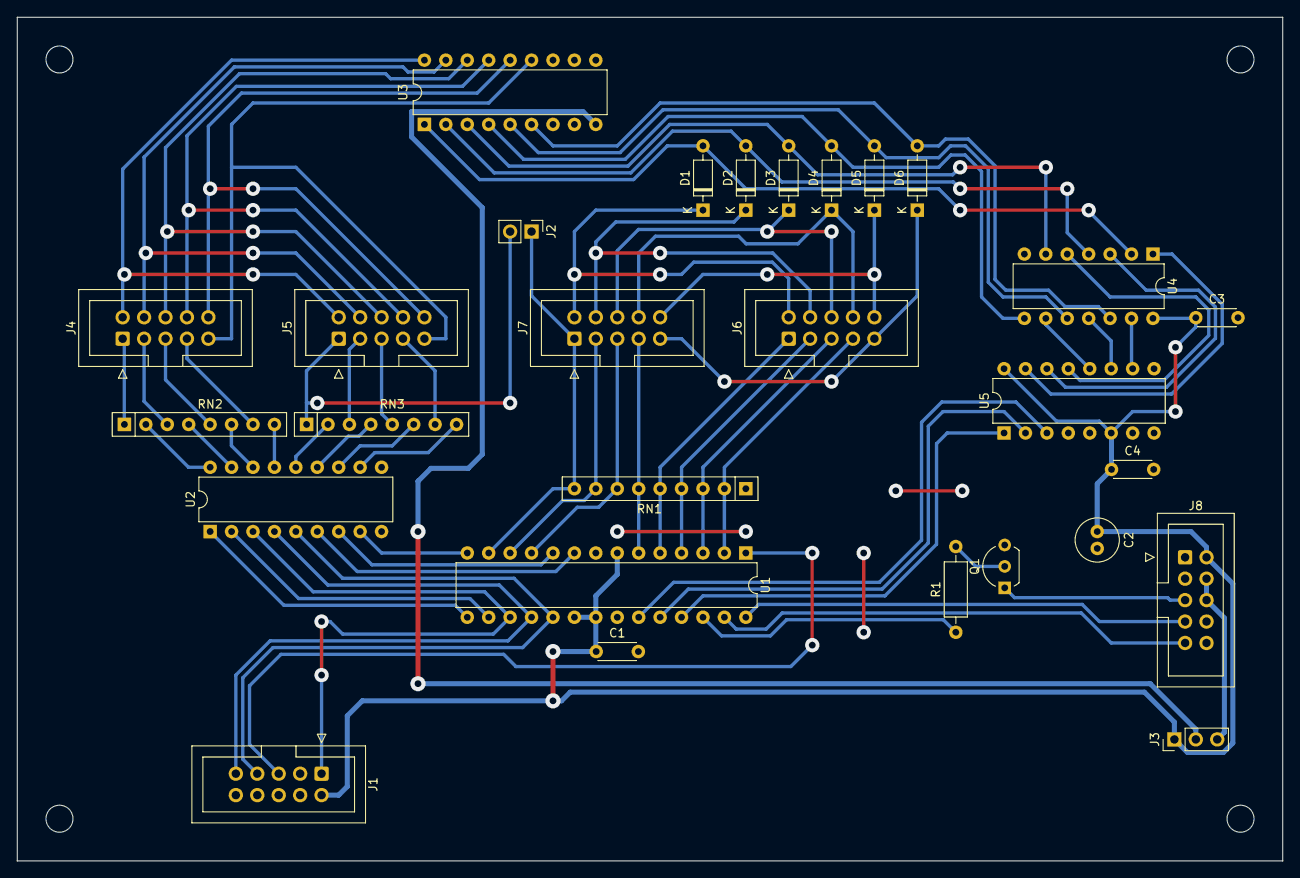
[picture p62: board PistonEncoder.kicad_pcb from above]

Board: 2 copper layers, 150.0 x 100.0 mm, 32 parts (0 on the bottom side), 69 nets.
