stefanhepp/eOrgan/boards/TechnicsEncoder/TechnicsEncoder.kicad_pcb

## KiCad design boards/TechnicsEncoder/TechnicsEncoder.kicad_pcb (2024-05-18)

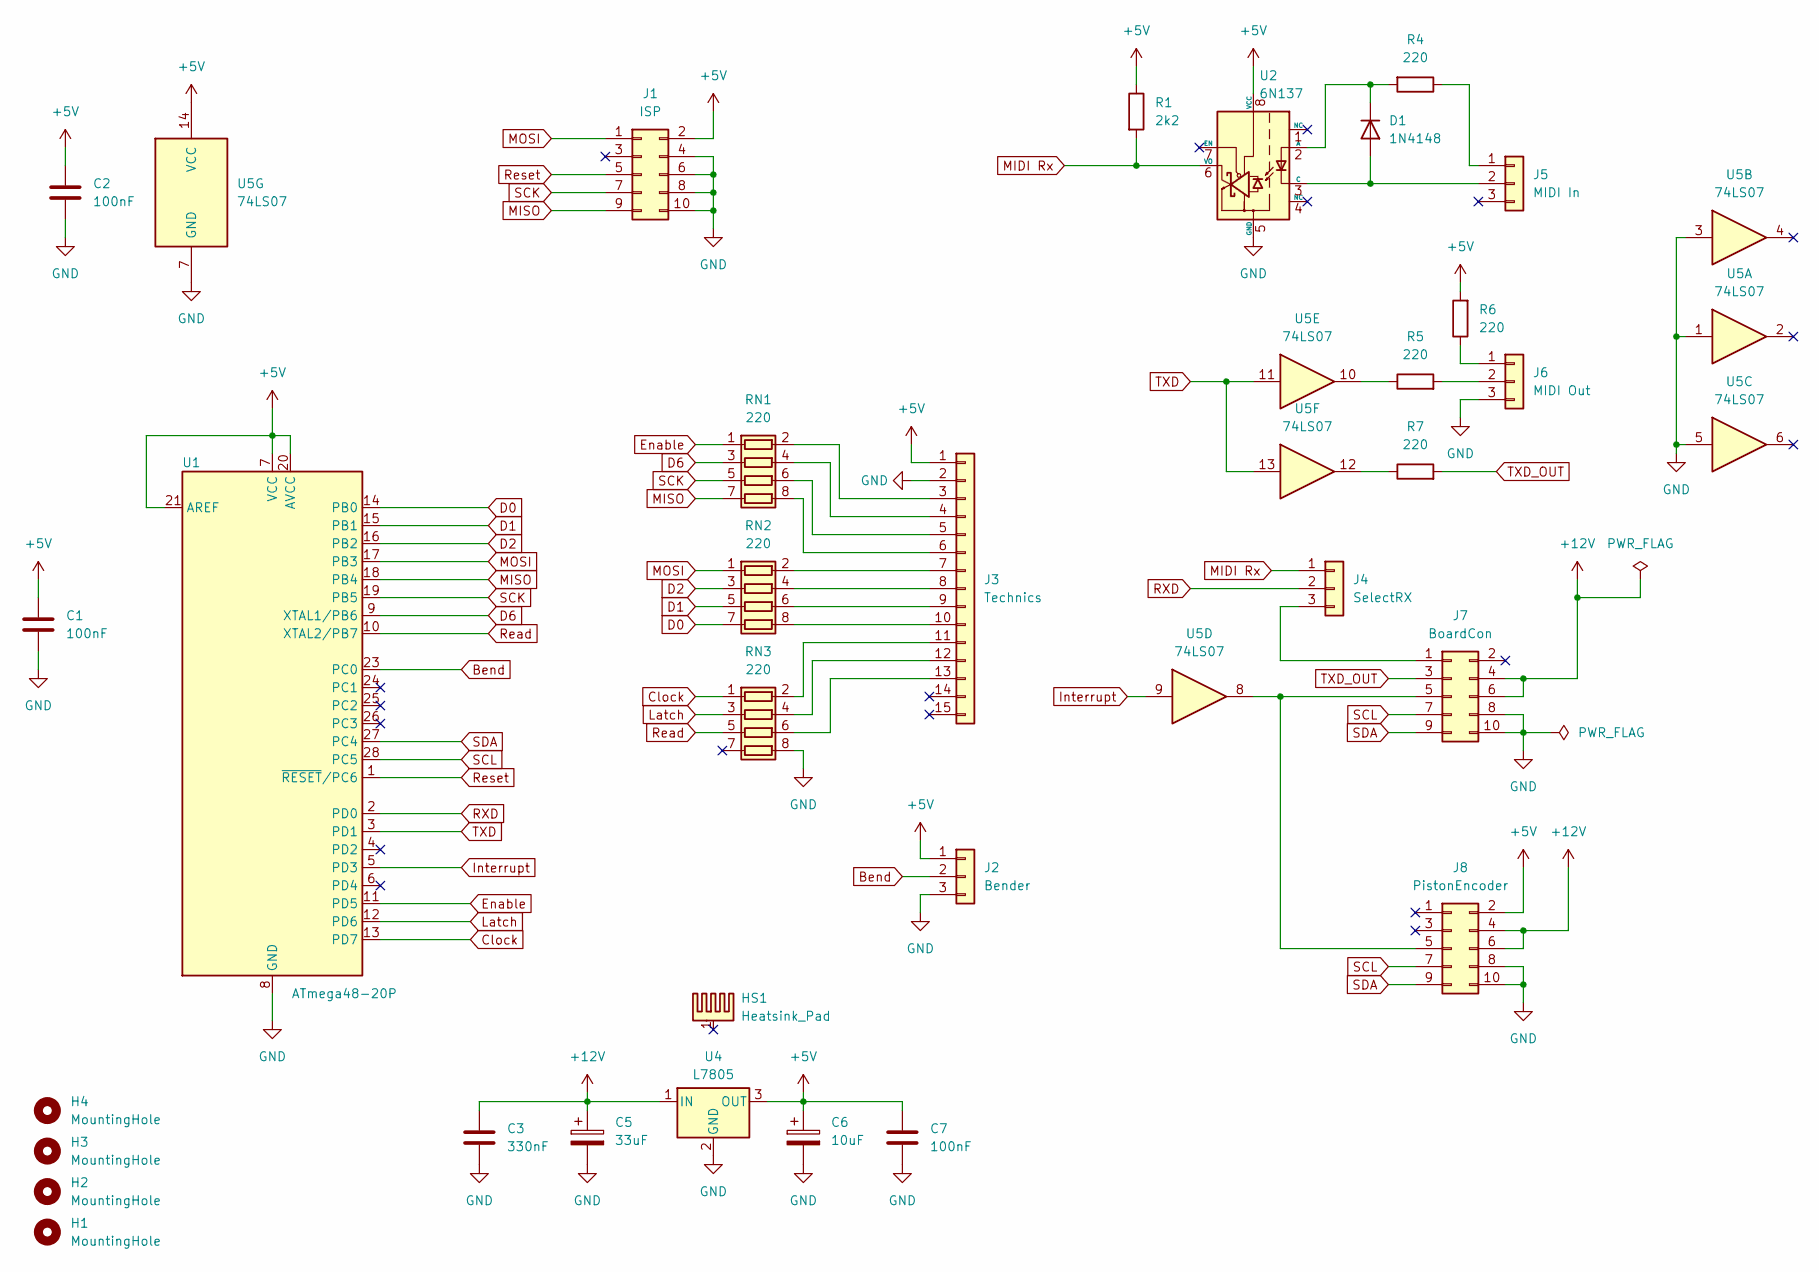
[picture p63: schematic TechnicsEncoder.kicad_sch]

Parts:
C1, C2, C7: 100nF; C_Disc_D4.3mm_W1.9mm_P5.00mm
C3: 330nF; C_Disc_D4.3mm_W1.9mm_P5.00mm
C5: 33uF; CP_Radial_D7.5mm_P2.50mm
C6: 10uF; CP_Radial_D6.3mm_P2.50mm
D1: 1N4148; D_DO-35_SOD27_P7.62mm_Horizontal
H1, H2, H3, H4: MountingHole; MountingHole_3mm
HS1: Heatsink_Pad; Heatsink_Aavid_TO-220_H12.7mm
J1: ISP; IDC-Header_2x05_P2.54mm_Vertical
J2: Bender; PinHeader_1x03_P2.54mm_Vertical
J3: Technics; JST_PH_B15B-PH-K_1x15_P2.00mm_Vertical
J4: SelectRX; PinHeader_1x03_P2.54mm_Vertical
J5: MIDI In; PinHeader_1x03_P2.54mm_Vertical
J6: MIDI Out; PinHeader_1x03_P2.54mm_Vertical
J7: BoardCon; IDC-Header_2x05_P2.54mm_Vertical
J8: PistonEncoder; IDC-Header_2x05_P2.54mm_Vertical
R1: 2k2; R_Axial_DIN0207_L6.3mm_D2.5mm_P2.54mm_Vertical
R4, R6: 220; R_Axial_DIN0207_L6.3mm_D2.5mm_P2.54mm_Vertical
R5, R7: 220; R_Axial_DIN0207_L6.3mm_D2.5mm_P10.16mm_Horizontal
RN1, RN2, RN3: 220; R_Array_SIP8
U1: ATmega48-20P; DIP-28_W7.62mm_Socket
U2: 6N137; DIP-8_W7.62mm
U4: L7805; TO-220-3_Vertical
U5: 74LS07; DIP-14_W7.62mm

Connections:
+5V: C1.1, C2.1, C6.1, C7.1, J1.2, J2.1, J3.1, J8.2, R1.1, R6.2, U1.7 (VCC), U1.20 (AVCC), U1.21 (AREF), U2.8 (VCC), U4.3 (OUT), U5.14 (VCC)
+12V: C3.1, C5.1, J7.4, J7.6, J8.4, J8.6, U4.1 (IN)
Bend: J2.2, U1.23 (PC0)
Clock: RN3.1 (R1.1), U1.13 (PD7)
D0: RN2.7 (R4.1), U1.14 (PB0)
D1: RN2.5 (R3.1), U1.15 (PB1)
D2: RN2.3 (R2.1), U1.16 (PB2)
D6: RN1.3 (R2.1), U1.9 (XTAL1/PB6)
Enable: RN1.1 (R1.1), U1.11 (PD5)
GND: C1.2, C2.2, C3.2, C5.2, C6.2, C7.2, J1.4, J1.6, J1.8, J1.10, J2.3, J3.2, J6.3, J7.8, J7.10, J8.8, J8.10, RN3.8 (R4.2), U1.8 (GND), U1.22 (GND), U2.5 (GND), U4.2 (GND), U5.1, U5.3, U5.5, U5.7 (GND)
Interrupt: U1.5 (PD3), U5.9
Latch: RN3.3 (R2.1), U1.12 (PD6)
MIDI Rx: J4.1, R1.2, U2.6 (VO)
MISO: J1.9, RN1.7 (R4.1), U1.18 (PB4)
MOSI: J1.1, RN2.1 (R1.1), U1.17 (PB3)
unnamed: D1.2 (A), J5.2, U2.3 (C)
unnamed: D1.1 (K), R4.2, U2.2 (A)
unnamed: J3.3, RN1.2 (R1.2)
unnamed: J3.4, RN1.4 (R2.2)
unnamed: J3.5, RN1.6 (R3.2)
unnamed: J3.6, RN1.8 (R4.2)
unnamed: J3.7, RN2.2 (R1.2)
unnamed: J3.8, RN2.4 (R2.2)
unnamed: J3.9, RN2.6 (R3.2)
unnamed: J3.10, RN2.8 (R4.2)
unnamed: J3.11, RN3.2 (R1.2)
unnamed: J3.12, RN3.4 (R2.2)
unnamed: J3.13, RN3.6 (R3.2)
unnamed: J4.3, J7.1
unnamed: J5.1, R4.1
unnamed: J6.1, R6.1
unnamed: J6.2, R5.2
unnamed: J7.5, J8.5, U5.8
unnamed: R5.1, U5.10
unnamed: R7.1, U5.12
RXD: J4.2, U1.2 (PD0)
Read: RN3.5 (R3.1), U1.10 (XTAL2/PB7)
Reset: J1.5, U1.1 (~RESET/PC6)
SCK: J1.7, RN1.5 (R3.1), U1.19 (PB5)
SCL: J7.7, J8.7, U1.28 (PC5)
SDA: J7.9, J8.9, U1.27 (PC4)
TXD: U1.3 (PD1), U5.11, U5.13
TXD_OUT: J7.3, R7.2

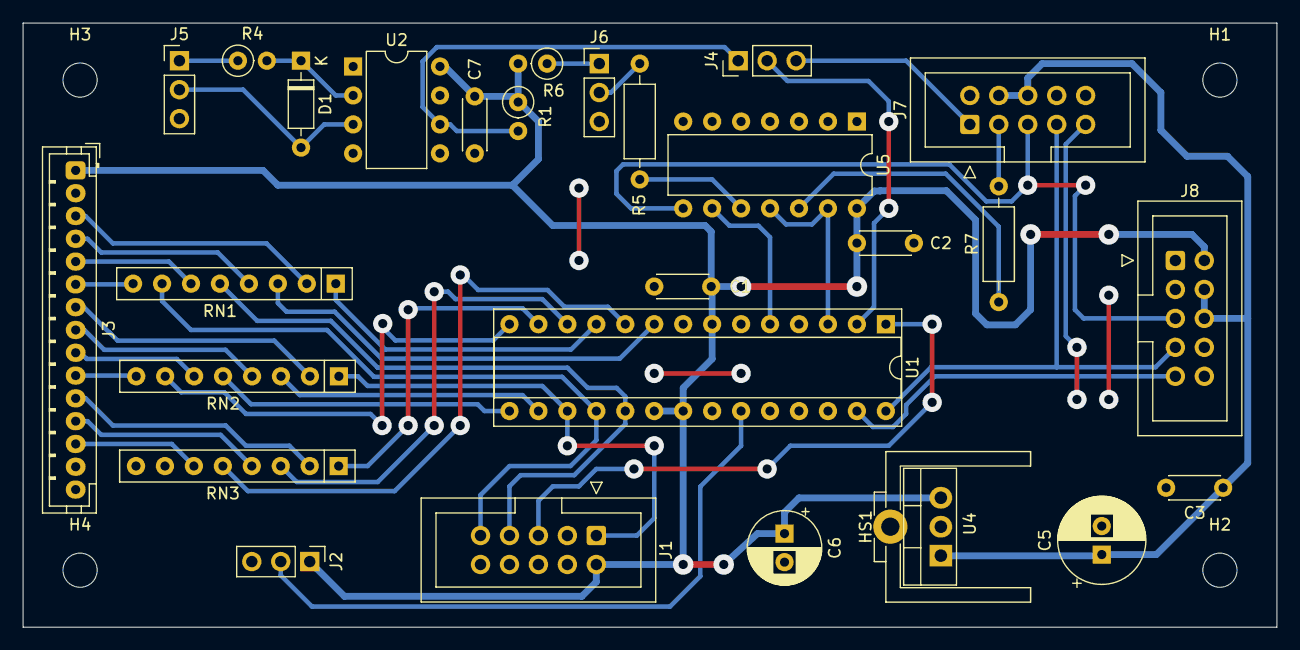
[picture p64: board TechnicsEncoder.kicad_pcb from above]

Board: 2 copper layers, 110.0 x 53.0 mm, 32 parts (0 on the bottom side), 43 nets.
