stefanhepp/eOrgan/boards/MIDIController-IO-MIDI/MIDIController-IO-MIDI.kicad_pcb

## KiCad design boards/MIDIController-IO-MIDI/MIDIController-IO-MIDI.kicad_pcb (2024-05-18)

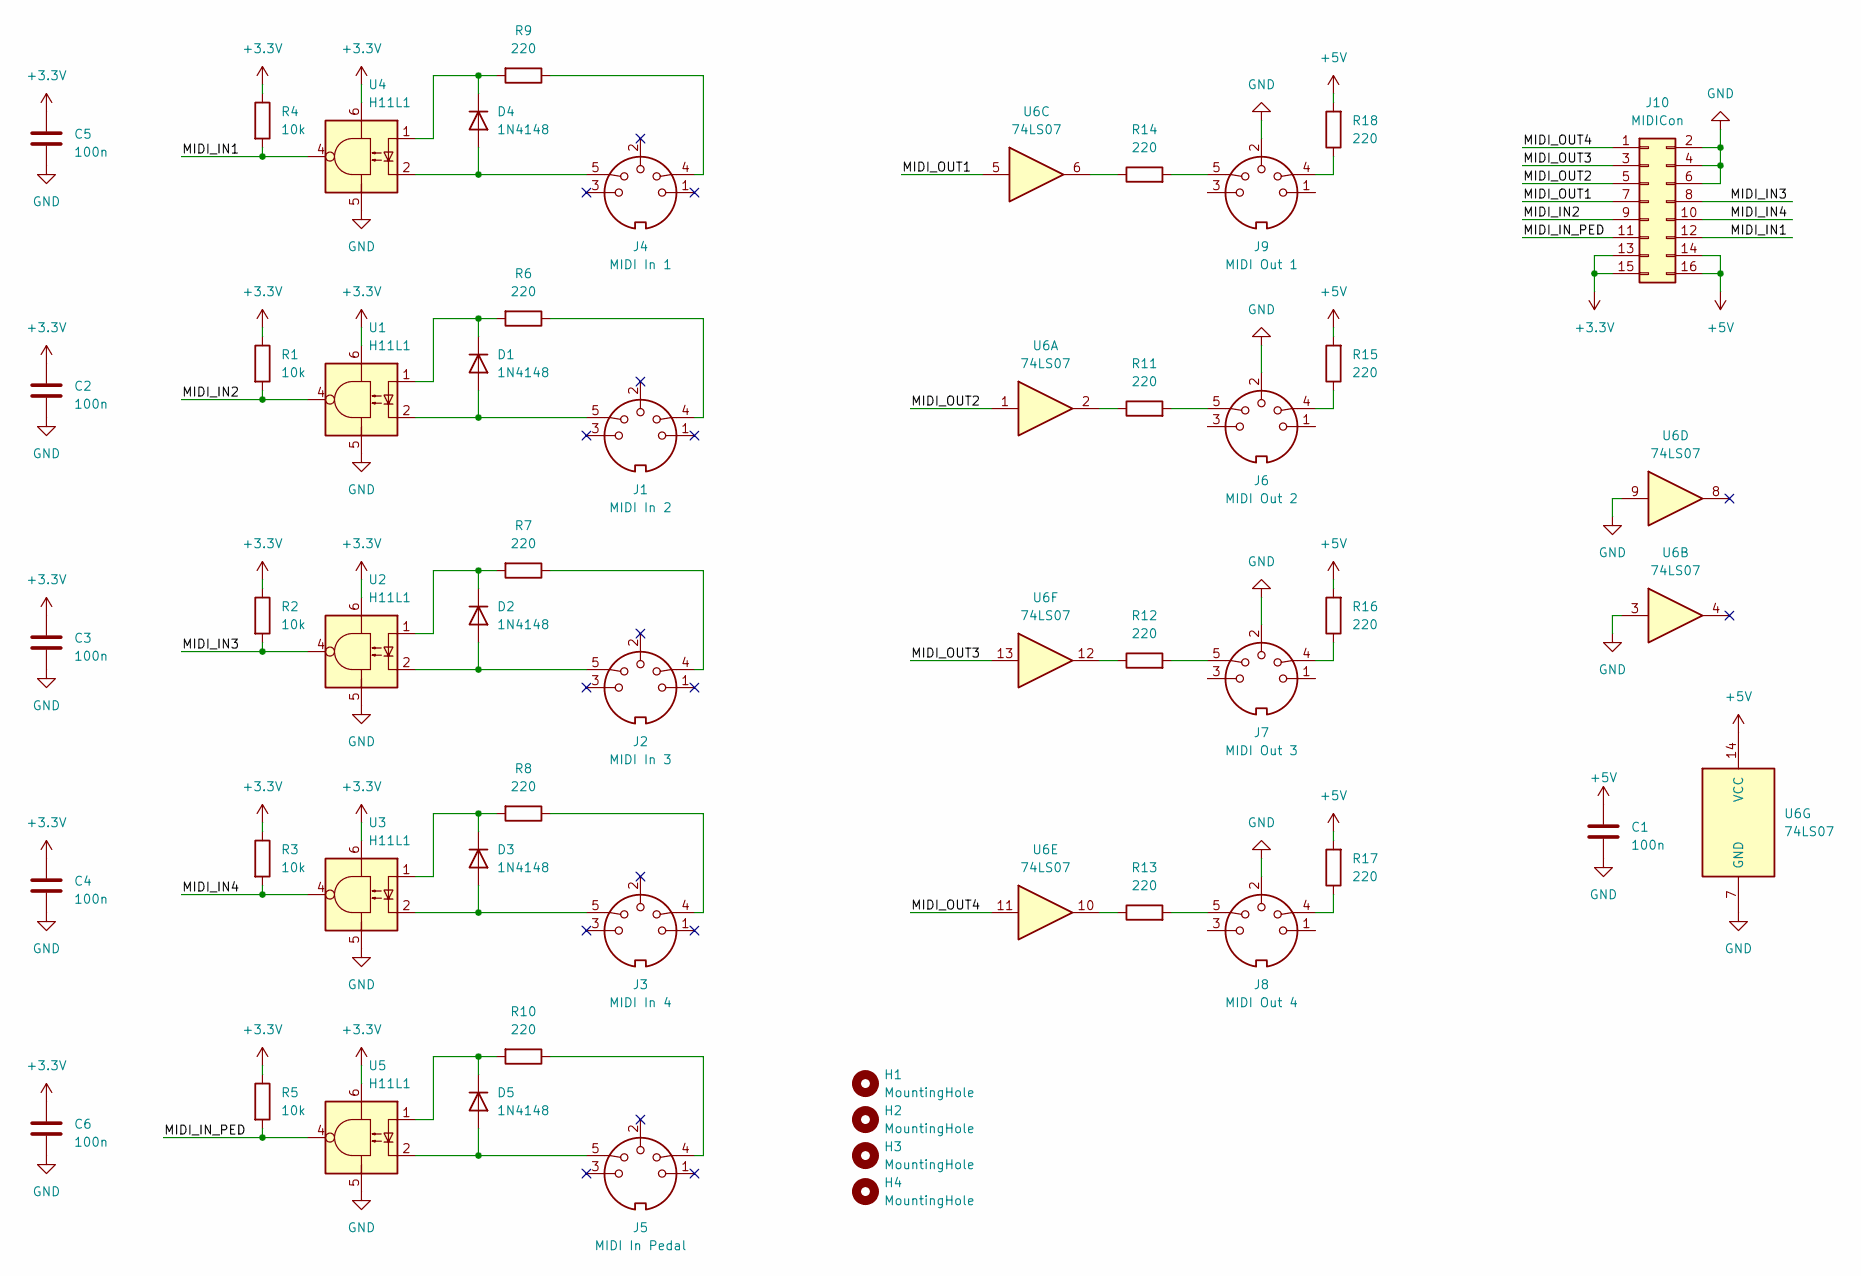
[picture p65: schematic MIDIController-IO-MIDI.kicad_sch]

Parts:
C1, C2, C3, C4, C5, C6: 100n; C_Disc_D5.0mm_W2.5mm_P5.00mm
D1, D2, D3, D4, D5: 1N4148; D_DO-35_SOD27_P7.62mm_Horizontal
H1, H2, H3, H4: MountingHole; MountingHole_3.2mm_M3
J1: MIDI In 2; DIN-5 MAB5P
J2: MIDI In 3; DIN-5 MAB5P
J3: MIDI In 4; DIN-5 MAB5P
J4: MIDI In 1; DIN-5 MAB5P
J5: MIDI In Pedal; DIN-5 MAB5P
J6: MIDI Out 2; DIN-5 MAB5P
J7: MIDI Out 3; DIN-5 MAB5P
J8: MIDI Out 4; DIN-5 MAB5P
J9: MIDI Out 1; DIN-5 MAB5P
J10: MIDICon; IDC-Header_2x08_P2.54mm_Vertical
R1, R2, R3, R4, R5: 10k; R_Axial_DIN0207_L6.3mm_D2.5mm_P10.16mm_Horizontal
R6, R7, R8, R9, R10, R11, R12, R13, R14, R15, R16, R17, R18: 220; R_Axial_DIN0207_L6.3mm_D2.5mm_P10.16mm_Horizontal
U1, U2, U3, U4, U5: H11L1; DIP-6_W7.62mm
U6: 74LS07; DIP-14_W7.62mm

Connections:
+3.3V: C2.1, C3.1, C4.1, C5.1, C6.1, J10.13, J10.15, R1.1, R2.1, R3.1, R4.1, R5.1, U1.6, U2.6, U3.6, U4.6, U5.6
+5V: C1.1, J10.14, J10.16, R15.2, R16.2, R17.2, R18.2, U6.14 (VCC)
/MIDI_IN1: J10.12, R4.2, U4.4
/MIDI_IN2: J10.9, R1.2, U1.4
/MIDI_IN3: J10.8, R2.2, U2.4
/MIDI_IN4: J10.10, R3.2, U3.4
/MIDI_IN_PED: J10.11, R5.2, U5.4
/MIDI_OUT1: J10.7, U6.5
/MIDI_OUT2: J10.5, U6.1
/MIDI_OUT3: J10.3, U6.13
/MIDI_OUT4: J10.1, U6.11
GND: C1.2, C2.2, C3.2, C4.2, C5.2, C6.2, J6.2, J7.2, J8.2, J9.2, J10.2, J10.4, J10.6, U1.5, U2.5, U3.5, U4.5, U5.5, U6.3, U6.7 (GND), U6.9
unnamed: D1.2 (A), J1.5, U1.2
unnamed: D1.1 (K), R6.2, U1.1
unnamed: D2.2 (A), J2.5, U2.2
unnamed: D2.1 (K), R7.2, U2.1
unnamed: D3.2 (A), J3.5, U3.2
unnamed: D3.1 (K), R8.2, U3.1
unnamed: D4.2 (A), J4.5, U4.2
unnamed: D4.1 (K), R9.2, U4.1
unnamed: D5.2 (A), J5.5, U5.2
unnamed: D5.1 (K), R10.2, U5.1
unnamed: J1.4, R6.1
unnamed: J2.4, R7.1
unnamed: J3.4, R8.1
unnamed: J4.4, R9.1
unnamed: J5.4, R10.1
unnamed: J6.4, R15.1
unnamed: J6.5, R11.2
unnamed: J7.4, R16.1
unnamed: J7.5, R12.2
unnamed: J8.4, R17.1
unnamed: J8.5, R13.2
unnamed: J9.4, R18.1
unnamed: J9.5, R14.2
unnamed: R11.1, U6.2
unnamed: R12.1, U6.12
unnamed: R13.1, U6.10
unnamed: R14.1, U6.6

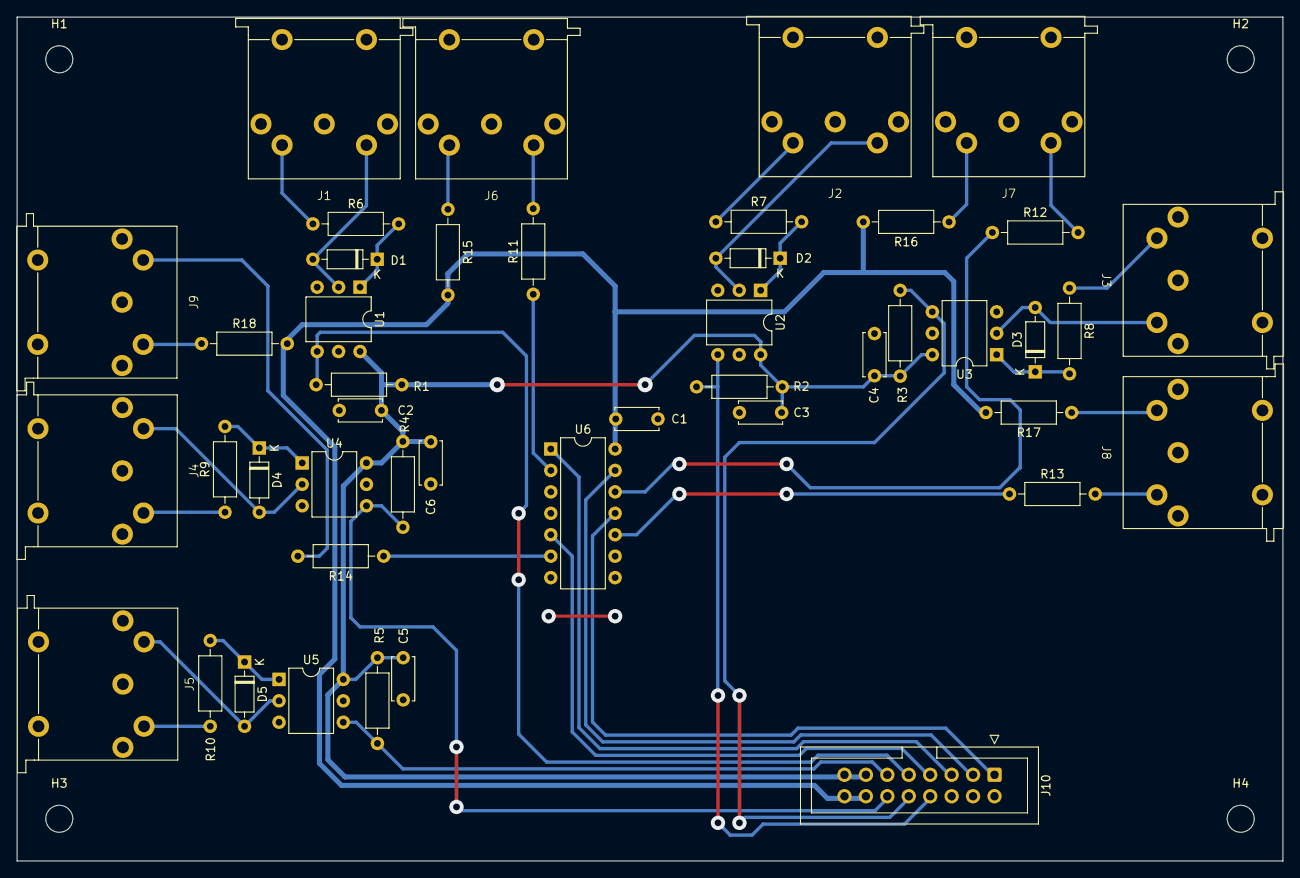
[picture p66: board MIDIController-IO-MIDI.kicad_pcb from above]

Board: 2 copper layers, 150.0 x 100.0 mm, 49 parts (0 on the bottom side), 39 nets.
