stefanhepp/eOrgan/boards/KeyboardShiftScanner/KeyboardShiftScanner.kicad_pcb

## KiCad design boards/KeyboardShiftScanner/KeyboardShiftScanner.kicad_pcb (2023-04-19)

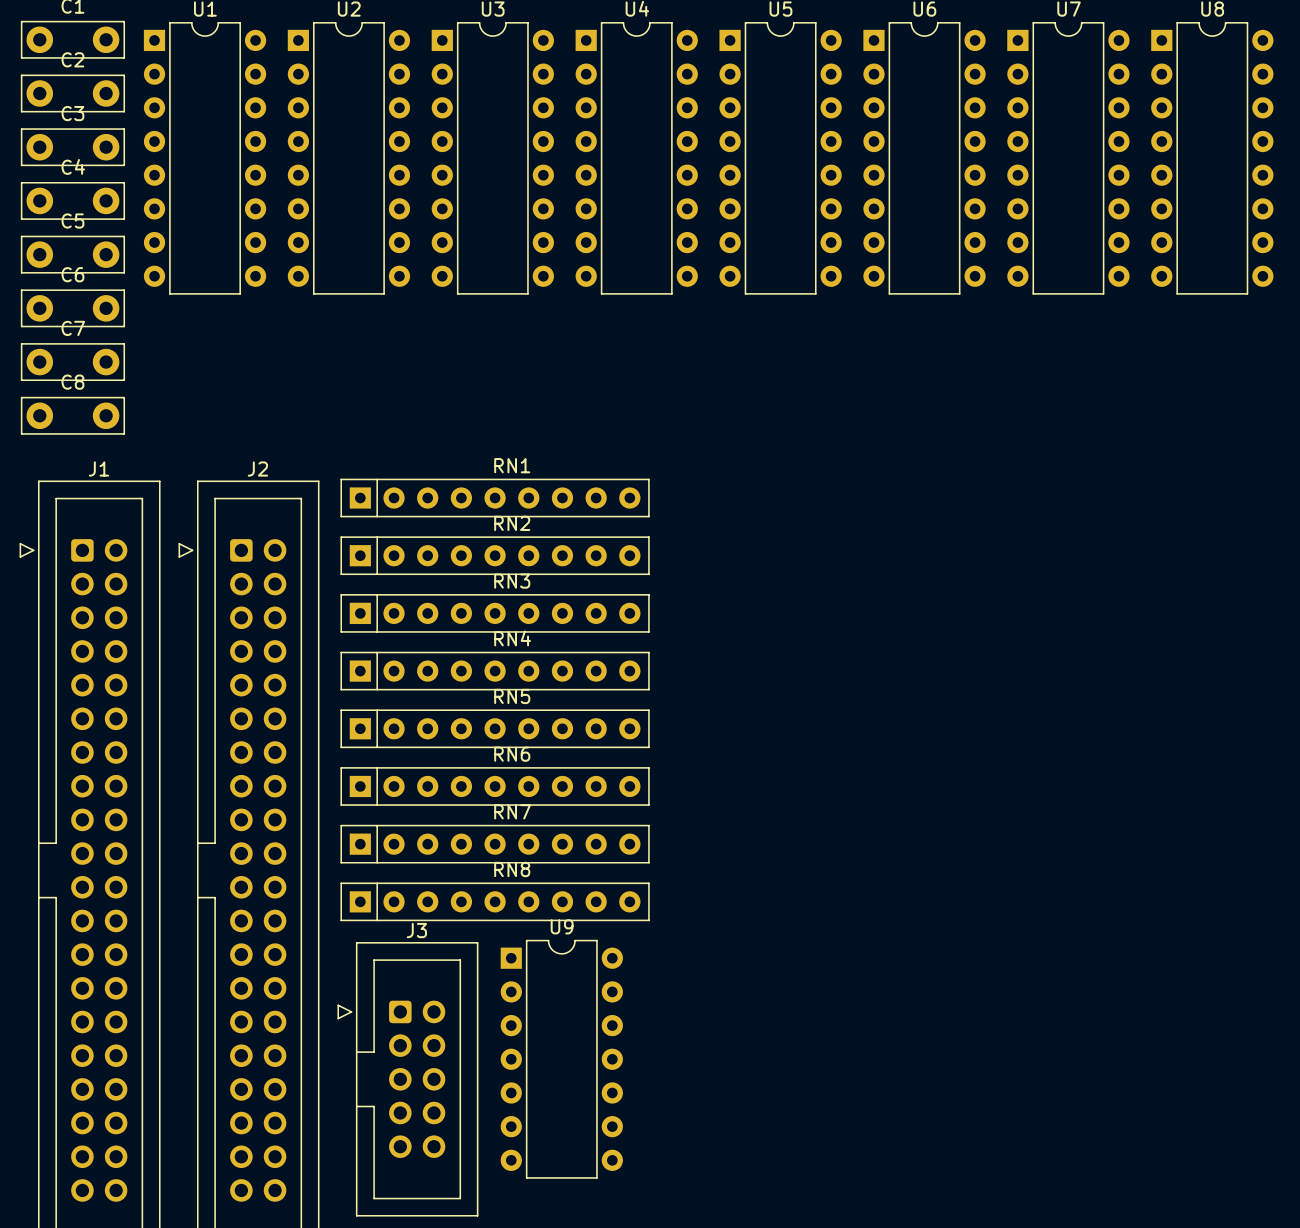
[picture p67: board KeyboardShiftScanner.kicad_pcb from above]

Board: 2 copper layers, 28 parts (0 on the bottom side), 80 nets, no tracks yet.

Parts:
C1, C2, C3, C4, C5, C6, C7, C8: 100nF; C_Disc_D7.5mm_W2.5mm_P5.00mm
J1, J2: Keyboard1; IDC-Header_2x20_P2.54mm_Vertical
J3: Encoder; IDC-Header_2x05_P2.54mm_Vertical
RN1, RN2, RN3, RN4, RN5, RN6, RN7, RN8: 10k; R_Array_SIP9
U1, U2, U3, U4, U5, U6, U7, U8: 4014; DIP-16_W7.62mm
U9: 4069; DIP-14_W7.62mm

Connections:
+5V: C1.1, C2.1, C3.1, C4.1, C5.1, C6.1, C7.1, C8.1, J1.21, J2.21, J3.2, J3.4, U1.16 (Vdd), U2.16 (Vdd), U3.16 (Vdd), U4.16 (Vdd), U5.16 (Vdd), U6.16 (Vdd), U7.16 (Vdd), U8.16 (Vdd), U9.7 (VSS)
CP: U1.10 (CP), U2.10 (CP), U3.10 (CP), U4.10 (CP), U5.10 (CP), U6.10 (CP), U7.10 (CP), U8.10 (CP), U9.4
GND: C1.2, C2.2, C3.2, C4.2, C5.2, C6.2, C7.2, C8.2, J3.8, J3.10, RN1.1 (common), RN2.1 (common), RN3.1 (common), RN4.1 (common), RN5.1 (common), RN6.1 (common), RN7.1 (common), RN8.1 (common), U1.8 (Vss), U1.11 (DS), U2.8 (Vss), U3.8 (Vss), U3.11 (DS), U4.8 (Vss), U5.8 (Vss), U5.11 (DS), U6.8 (Vss), U7.8 (Vss), U7.11 (DS), U8.8 (Vss), U9.5, U9.13, U9.14 (VDD)
K01: J1.1, RN3.9 (R8), U1.7 (P0)
K02: J1.3, RN3.8 (R7), U1.6 (P1)
K03: J1.5, RN3.7 (R6), U1.5 (P2)
K04: J1.7, RN3.6 (R5), U1.4 (P3)
K05: J1.9, RN3.5 (R4), U1.13 (P4)
K06: J1.11, RN3.4 (R3), U1.14 (P5)
K07: J1.13, RN3.3 (R2), U1.15 (P6)
K08: J1.15, RN3.2 (R1), U1.1 (P7)
K09: J1.25, RN1.9 (R8), U2.7 (P0)
K10: J1.27, RN1.8 (R7), U2.6 (P1)
K11: J1.29, RN1.7 (R6), U2.5 (P2)
K12: J1.31, RN1.6 (R5), U2.4 (P3)
K13: J1.33, RN1.5 (R4), U2.13 (P4)
K14: J1.35, RN1.4 (R3), U2.14 (P5)
K15: J1.37, RN1.3 (R2), U2.15 (P6)
K16: J1.39, RN1.2 (R1), U2.1 (P7)
K17: J2.1, RN4.9 (R8), U3.7 (P0)
K18: J2.3, RN4.8 (R7), U3.6 (P1)
K19: J2.5, RN4.7 (R6), U3.5 (P2)
K20: J2.7, RN4.6 (R5), U3.4 (P3)
K21: J2.9, RN4.5 (R4), U3.13 (P4)
K22: J2.11, RN4.4 (R3), U3.14 (P5)
K23: J2.13, RN4.3 (R2), U3.15 (P6)
K24: J2.15, RN4.2 (R1), U3.1 (P7)
K25: J2.25, RN2.9 (R8), U4.7 (P0)
K26: J2.27, RN2.8 (R7), U4.6 (P1)
K27: J2.29, RN2.7 (R6), U4.5 (P2)
K28: J2.31, RN2.6 (R5), U4.4 (P3)
K29: J2.33, RN2.5 (R4), U4.13 (P4)
K30: J2.35, RN2.4 (R3), U4.14 (P5)
K31: J2.37, RN2.3 (R2), U4.15 (P6)
K32: J2.39, RN2.2 (R1), U4.1 (P7)
K33: J1.2, RN5.2 (R1), U5.7 (P0)
K34: J1.4, RN5.3 (R2), U5.6 (P1)
K35: J1.6, RN5.4 (R3), U5.5 (P2)
K36: J1.8, RN5.5 (R4), U5.4 (P3)
K37: J1.10, RN5.6 (R5), U5.13 (P4)
K38: J1.12, RN5.7 (R6), U5.14 (P5)
K39: J1.14, RN5.8 (R7), U5.15 (P6)
K40: J1.16, RN5.9 (R8), U5.1 (P7)
K41: J1.26, RN6.9 (R8), U6.7 (P0)
K42: J1.28, RN6.8 (R7), U6.6 (P1)
K43: J1.30, RN6.7 (R6), U6.5 (P2)
K44: J1.32, RN6.6 (R5), U6.4 (P3)
K45: J1.34, RN6.5 (R4), U6.13 (P4)
K46: J1.36, RN6.4 (R3), U6.14 (P5)
K47: J1.38, RN6.3 (R2), U6.15 (P6)
K48: J1.40, RN6.2 (R1), U6.1 (P7)
K49: J2.2, RN7.2 (R1), U7.7 (P0)
K50: J2.4, RN7.3 (R2), U7.6 (P1)
K51: J2.6, RN7.4 (R3), U7.5 (P2)
K52: J2.8, RN7.5 (R4), U7.4 (P3)
K53: J2.10, RN7.6 (R5), U7.13 (P4)
K54: J2.12, RN7.7 (R6), U7.14 (P5)
K55: J2.14, RN7.8 (R7), U7.15 (P6)
K56: J2.16, RN7.9 (R8), U7.1 (P7)
K57: J2.26, RN8.9 (R8), U8.7 (P0)
K58: J2.28, RN8.8 (R7), U8.6 (P1)
K59: J2.30, RN8.7 (R6), U8.5 (P2)
K60: J2.32, RN8.6 (R5), U8.4 (P3)
K61: J2.34, RN8.5 (R4), U8.13 (P4)
K62: J2.36, RN8.4 (R3), U8.14 (P5)
K63: J2.38, RN8.3 (R2), U8.15 (P6)
K64: J2.40, RN8.2 (R1), U8.1 (P7)
unnamed: J3.1, U9.1
unnamed: J3.6, U9.11
unnamed: U1.3 (Q7), U2.11 (DS)
unnamed: U3.3 (Q7), U4.11 (DS)
unnamed: U5.3 (Q7), U6.11 (DS)
unnamed: U7.3 (Q7), U8.11 (DS)
unnamed: U9.2, U9.3
unnamed: U9.9, U9.10
PL: U1.9 (PL), U2.9 (PL), U3.9 (PL), U4.9 (PL), U5.9 (PL), U6.9 (PL), U7.9 (PL), U8.9 (PL), U9.8
S1: J3.3, U2.3 (Q7)
S2: J3.5, U4.3 (Q7)
S3: J3.7, U6.3 (Q7)
S4: J3.9, U8.3 (Q7)
