stefanhepp/eOrgan/boards/SwellEncoder/SwellEncoder.kicad_pcb

## KiCad design boards/SwellEncoder/SwellEncoder.kicad_pcb (2022-11-13)

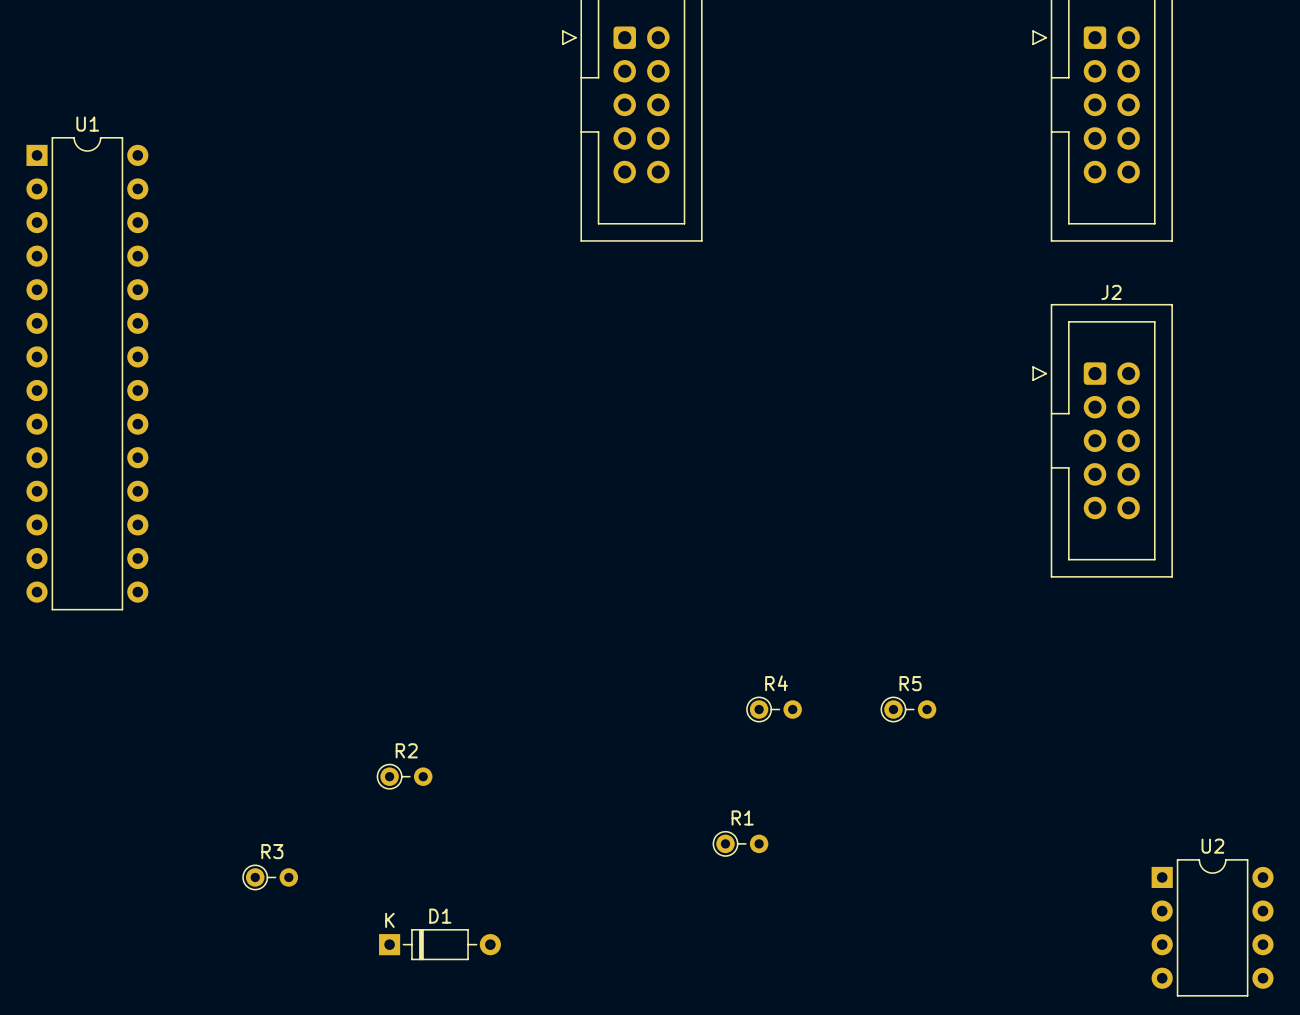
[picture p68: board SwellEncoder.kicad_pcb from above]

Board: 2 copper layers, 11 parts (0 on the bottom side), 19 nets, no tracks yet.

Parts:
D1: 1N4148; D_DO-35_SOD27_P7.62mm_Horizontal
J2: ISP; IDC-Header_2x05_P2.54mm_Vertical
J3: ToeLeft; IDC-Header_2x05_P2.54mm_Vertical
J4: ToeRight; IDC-Header_2x05_P2.54mm_Vertical
R1: 10k; R_Axial_DIN0204_L3.6mm_D1.6mm_P2.54mm_Vertical
R2, R3, R4, R5: 220; R_Axial_DIN0204_L3.6mm_D1.6mm_P2.54mm_Vertical
U1: ATmega48-20P; DIP-28_W7.62mm
U2: 6N138; DIP-8_W7.62mm

Connections:
+5V: J2.2, R1.1, R4.2, U1.7 (VCC), U1.20 (AVCC), U1.21 (AREF), U2.8 (VCC)
GND: J2.4, J2.6, J2.8, J2.10, U1.8 (GND), U1.22 (GND), U2.5 (GND)
Interrupt: R2.1, U1.26 (PC3)
L1: J4.10, U1.14 (PB0)
L2: J4.8, U1.15 (PB1)
L3: J3.10, U1.16 (PB2)
MISO: J2.9, U1.18 (PB4)
MOSI: J2.1, J3.8, U1.17 (PB3)
unnamed: D1.1 (K), R5.2, U2.2 (C1)
unnamed: D1.2 (A), U2.3 (C2)
unnamed: J3.1, J4.1, U1.5 (PD3)
unnamed: J3.3, J4.3, U1.6 (PD4)
unnamed: J3.5, J4.5, U1.11 (PD5)
unnamed: J3.7, J4.7, U1.12 (PD6)
unnamed: J3.9, J4.9, U1.13 (PD7)
RXD: R1.2, U1.2 (PD0), U2.6 (VO2)
Reset: J2.5, U1.1 (~RESET/PC6)
SCK: J2.7, U1.19 (PB5)
TXD: R3.1, U1.3 (PD1)
